joe-scotto/scottokeebs/Scotto63/README.md

# Scotto63 (SK25)

The Scotto63 is a 63-key 60% split-monoblock column-staggered ortholinear ergonomic wireless keyboard with a large 750mah battery.

You can read more about the components and how to build it [here](https://scottokeebs.com/blogs/keyboards/scotto63-handwired-keyboard).

Scotto63
