joe-scotto/scottokeebs/ScottoDeck/README.md

# ScottoDeck (SK24)

The ScottoDeck is an 8-key macropad with two EC11 encoders designed for live streaming.

You can read more about the components and how to build it [here](https://scottokeebs.com/blogs/macropads/scottodeck-handwired-macropad).

ScottoDeck
