joe-scotto/scottokeebs/ScottoNum/README.md

# ScottoNum (SK14)

The ScottoNum is a 17-key wireless macropad.

You can read more about the components and how to build it [here](https://scottokeebs.com/blogs/macropads/scottonum-handwired-macropad).

ScottoNum
