joe-scotto/scottokeebs/Extras/ScottoKicad/README.md

# ScottoKicad

A collection of footprints, symbols, and 3D models for building mechanical keyboards with Kicad.

```diff
- I used to recommend only using Kicad 8 but Kicad 10 is fine and fixed many issues that came up in 9.
- Please read all installation instructions carefully!
```
# Installation

1. Add a `SCOTTOKEEBS_KICAD` path to match where the `ScottoKicad` folder is located.
   Preferences -> Configure Paths
   Configure Paths

2. Add the symbol library.
   Preferences -> Manage Symbol Libraries
   Symbol Libraries

3. Add the footprint libraries.
   Preferences -> Manage Footprint Libraries
   Footprint Libraries      

4. Ensure hotkeys match tutorial.
   Settings
   Import hotkeys
   CleanShot 2025-06-30 at 11 00 42@2x
   
5. Match Scotto Configuration (Optional).
   Settings
   Reveal
   Preferences
   Theme

6. That's it, you should now have everything you need!

# Common grid sizes

-   18x17mm (Choc)
    -   1.00u - X: 18, Y:17
    -   0.50u - X: 9, Y: 8.5
    -   0.25u - X: 4.5, Y: 4.25
-   19.05x19.05 (MX/Alps)
    -   1.00u - X: 19.05, Y: 19.05
    -   0.50u - X: 9.525, Y: 9.525
    -   0.25u X: 4.7625, Y: 4.7625

# Common Shortcuts

-   **Add (A)** - Add a footprint or symbol.
-   **Set Origin Point (S)** - Set where everything else will move in relation to.
-   **Move with Reference (])** - Move a footprint with a reference point.
-   **Track Tool (X)** - Place traces
-   **Add Via (V)** - Place a via to run a trace between PCB layers.
-   **Flip (F)** - Switch footprint between back and front of the PCB.

# Resources

Please refer to each library in order to understand the license it uses, most are Creative Commons CC-BY-SA 4.0.

-   [Keyswitch Library](https://github.com/kiswitch/kiswitch/tree/main) - 3D models and footprints for switches, stabilizers, and sockets.
-   [Raspberry Pi Pico](https://github.com/ncarandini/KiCad-RP-Pico) - 3D model, footprint, and symbol.
-   [Arduino Pro Micro](https://github.com/g200kg/kicad-lib-arduino) - Footprint and symbol.
-   [Marbastlib](https://github.com/ebastler/marbastlib) - Symbols.
-   [Kleeb](https://github.com/crides/kleeb) - 3D models, symbols, and footprints.
-   [Keebio](https://github.com/keebio/Keebio-Parts.pretty) - 3D models, footprints, and symbols.
-   [Adafruit](https://github.com/adafruit/Adafruit_CAD_Parts/tree/main?tab=MIT-1-ov-file#readme) - 3D models

# Credits

Feel free to reach out to me on Discord if you want to help get a component into the library.

-   nice!nano - Base dimensions and placement by @Knotherface, can be found on GitHub as [Leopere](https://github.com/Leopere).
