joe-scotto/scottokeebs/ScottoRang/PCB/README.md

# ScottoRang (PCB Edition) (SK41)

The ScottoRang (PCB Edition) is a 34-key split monoblock ergonomic 16x16mm Choc spaced keyboard with a central 128x64 OLED display.

You can read more about the components and how to build it [here](https://scottokeebs.com/blogs/keyboards/scottorang-pcb-keyboard).

ScottoRang (PCB Editioin)

# Proudly Sponsored by [NextPCB](https://nextpcb.com)

Thanks to NextPCB for providing the PCBs for this project. Make sure to check them out for high quality PCB and PCBA services!
