joe-scotto/scottokeebs/ScottoT9/PCB/README.md

# ScottoT9 (SK39)

The ScottoT9 (PCB Edition) is a 14-key macropad based on the T9 keyboard layout with a 128x64 OLED display.

You can read more about the components and how to build it [here](https://scottokeebs.com/blogs/macropads/scottot9-pcb-macropad).

ScottoT9 (PCB Edition)

# Proudly Sponsored by [NextPCB](https://nextpcb.com)

Thanks to NextPCB for providing the PCBs for this project. Make sure to check them out for high quality PCB and PCBA services!
