joe-scotto/scottokeebs/Extras/ScottoShrink/README.md

# ScottoShrink

A tool for cutting perfect 8mm long pieces of heat shrink tubing.
