joe-scotto/scottokeebs/ScottoFrog/PCB/README.md

# ScottoFrog (SK37)

A 20-key single handed keyboard based on the [Frogpad](http://frogpad.com).

You can read more about the components and how to build it [here](https://scottokeebs.com/blogs/macropads/scottofrog-PCB-macropad).

ScottoFrog (PCB Edition

# Proudly Sponsored by [NextPCB](https://nextpcb.com)

Thanks to NextPCB for providing the PCBs for this project. Make sure to check them out for high quality PCB and PCBA services!
