joe-scotto/scottokeebs/ScottoT9/Handwired/README.md

# ScottoT9 (SK38)

The ScottoT9 is a 12-key macropad based on the T9 keyboard layout.

You can read more about the components and how to build it [here](https://scottokeebs.com/blogs/macropads/scottot9-handwired-macropad).

ScottoT9
