joe-scotto/scottokeebs/ScottoKatana/PCB/README.md

# ScottoKatana (PCB Edition) (SK35)

The ScottoKatana (PCB Edition) is a 35-key katana staggered keyboard with a 7u spacebar, 128x64 OLED, 6 RGB LEDs, and four 1.25u function keys.

You can read more about the components and how to build it [here](https://scottokeebs.com/blogs/keyboards/scottokatana-pcb-keyboard).

ScottoKatana (PCB Edition)

# Proudly Sponsored by [NextPCB](https://nextpcb.com)

Thanks to NextPCB for providing the PCBs for this project. Make sure to check them out for high quality PCB and PCBA services!
