joe-scotto/scottokeebs/Scotto69/PCB/README.md

# Scotto69 (PCB Edition) (SK30)

The Scotto69 (PCB Edition) is a standard 4x12 ortholinear keyboard with a numpad on the right and 5 macro keys on the left with an optional encoder.

You can read more about the components and how to build it [here](https://scottokeebs.com/blogs/keyboards/scotto69-pcb-keyboard).

Scotto69 (PCB Edition)
