joe-scotto/scottokeebs/ScottoSlant/PCB/README.md

# ScottoSlant (PCB Edition) (SK29)

The ScottoSlant is a 38-key 0.25u row-staggered keyboard with a split 2u spacebar.

You can read more about the components and how to build it [here](https://scottokeebs.com/blogs/keyboards/scottoslant-pcb-keyboard).

ScottoSlant (PCB Edition)
