joe-scotto/scottokeebs/Scotto34/PCB/README.md

# Scotto34 (PCB Edition) (SK19)

The Scotto34 (PCB Edition) is a low-profile 34-key split monoblock ortholinear keyboard that uses 18x17mm spaced Choc switches and an exposed controller in the middle.

You can read more about the components and how to build it [here](https://scottokeebs.com/blogs/keyboards/scotto34-pcb-keyboard).

Scotto34 (PCB Edition)
