joe-scotto/scottokeebs/ScottoWing/PCB/README.md

# ScottoWing (PCB Edition) (SK26)

The ScottoWing (PCB Edition) is a 3x5 (34-keys) or 3x6 (40-keys) split monoblock ergonomic column-staggered keyboard.

You can read more about the components and how to build it [here](https://scottokeebs.com/blogs/keyboards/scottowing-pcb-keyboard).

ScottoWing (PCB Edition)
