joe-scotto/scottokeebs/Extras/ScottoCoiler/README.md

# ScottoCoiler

Diode coiling jig for handwired builds. You will need [16g](https://amzn.to/3OyQrq8) wire in order to build it, along with some glue and [3x2mm round magnets](https://amzn.to/457QPnh). 

Alternatively, you can purchase a pre-built one [here](https://scottokeebs.com/products/diode-coiling-jig).

ScottoCoiler
