joe-scotto/scottokeebs/Extras/ScottoLube/README.md

# ScottoLube

ScottoLube

A lube station with space for 36 MX switches, just enough for most of my boards.
