joe-scotto/scottokeebs/ScottoAlp/KMK/README.md

# ScottoAlp

ScottoAlp

Please refer to the [ScottoAlp](https://github.com/joe-scotto/scottokeebs/tree/main/ScottoAlp) GitHub page for more information.

# Microcontroller Support

In `kb.py` file, replace `boardsource_blok` in the following line with a supported microcontroller listed in `kmk/quickpin/pro_micro`:

```python
from kmk.quickpin.pro_micro.boardsource_blok import pinout as pins
```
