joe-scotto/scottokeebs/Extras/ScottoCaps/Scooped/Readme.md

# ScottoCaps (Scooped)

Scooped Cherry MX and Choc keycaps designed for FDM 3D printing. The legend variant of these are specifically designed for a printer capable of dual extrusion, you cannot print the legends on a single extruder printer. I recommend putting the back of the keycap towards the build plate. By doing this, you'll hide any texture on the back of the cap where it won't be as visible.

-   **Legends:** Gotham Rounded (Bold)
-   **Legend Height:** ~6mm
-   **Legend Depth:** 1.6mm
-   **Blank Scoop:** 1.0mm
-   **Keycap Dimensions:** 18.3x18.3x7.4mm (17.5x16.5x4.8mm or 17.5x17.5x4.8mm) 
-   **Keycap Spacing:** 0.75mm (0.50mm Choc)
-   **Corner Fillet:** 1.25mm
-   **Top Fillet:** 0.625mm

ScottoCaps (Scooped) Bambu Studio

# Stems

The stems are designed based on a tolerance of ~0.15mm, your printer may or may not be capable of handling this. If your keycaps are too tight, you can use some hot water to make the plastic more pliable when installing them. If they are too loose, you can cut [Kapton tape](https://amzn.to/45GeFFr) and use it between the keycap and switch to improve the fit.

This same method will apply to the stabilizers and is more likely to be needed as they're not all made equal. I've found some stabilizers are a lot smaller than the Cherry MX stem specifications which in turn requires more than one piece of tape to get them properly attached.

**Don't force them onto your switches as if they're too tight, it will be very hard to get them off.**

Taped Stem
