joe-scotto/scottokeebs/ScottoWing/Handwired/QMK/readme.md

# ScottoWing

ScottoWing

A low-profile 34/40-key split monoblock ergonomic column-staggered ortholinear keyboard that uses 18x17mm spaced Choc switches.

*   Keyboard Maintainer: [Joe Scotto](https://github.com/joe-scotto)
*   Hardware Supported: RP2040 ero
*   Hardware Availability: [ScottoKeebs](https://scottokeebs.com), [Amazon](https://amazon.com), [AliExpress](https://aliexpress.com)

# Compiling

Make example for this keyboard (after setting up your build environment):

    make scottokeebs/handwired/scottowing:default

Flashing example for this keyboard:

    make scottokeebs/handwired/scottowing:default:flash

See the [build environment setup](https://docs.qmk.fm/#/getting_started_build_tools) and the [make instructions](https://docs.qmk.fm/#/getting_started_make_guide) for more information. Brand new to QMK? Start with our [Complete Newbs Guide](https://docs.qmk.fm/#/newbs).

# Bootloader

Enter the bootloader in 3 ways:

*   **Bootmagic reset**: Hold down the key at (0,1) in the matrix (usually the top left key or Escape) and plug in the keyboard
*   **Physical reset button**: Briefly press the button on the back of the PCB - some may have pads you must short instead
*   **Keycode in layout**: Press the key mapped to `QK_BOOT` if it is available
