joe-scotto/scottokeebs/Extras/ScottoCaps/Glass/README.md

# ScottoCaps (Glass)

Low-profile flat keycaps designed for MSLA 3D printing compatible with MX and Choc switches. Designed to print flat on the build plate and tolerances may require modification depending on your printer.

**These must be printed in a bio-compatible 3D printing resin such as [Siraya Tech Blu](https://amzn.to/3seh5Nt)**

ScottoCaps on Scotto34 (PCB Edition)
