joe-scotto/scottokeebs/ScottoErgo/README.md

# ScottoErgo (SK16)

The ScottoErgo a 36-key column staggered ortholinear ergonomic keyboard with an exposed controller, aviator connector for USB, 10° of tilt, and 20° of angle.

You can read more about the components and how to build it [here](https://scottokeebs.com/blogs/keyboards/scottoergo-handwired-keyboard).

ScottoErgo
