joe-scotto/scottokeebs/ScottoGame/README.md

# ScottoGame (SK6)

The ScottoGame is a 42-key ortholinear keyboard with a dedicated action button, split spacebar, 5 function keys, and a 0.96" 128x64 OLED display.

You can read more about the components and how to build it [here](https://scottokeebs.com/blogs/keyboards/scottogame-handwired-keyboard).

ScottoGame
