joe-scotto/scottokeebs/ScottoSplit/README.md

# ScottoSplit (SK12)

The ScottoSplit is a 36-key split column-staggered ortholinear keyboard that uses a single MCU and VGA cable to connect the halves.

You can read more about the components and how to build it [here](https://scottokeebs.com/blogs/keyboards/scottosplit-handwired-keyboard).

ScottoSplit
