joe-scotto/scottokeebs/Scotto34/Handwired/README.md

# Scotto34 (SK13)

The Scotto34 is a low-profile 34-key split monoblock ortholinear keyboard that uses 18x17mm spaced Choc switches and an exposed controller in the middle.

You can read more about the components and how to build it [here](https://scottokeebs.com/blogs/keyboards/Scotto34-handwired-keyboard).

Scotto34
