joe-scotto/scottokeebs/Extras/ScottoCaps/Scooped/MX/Legends/Shift (1.50u).3mf

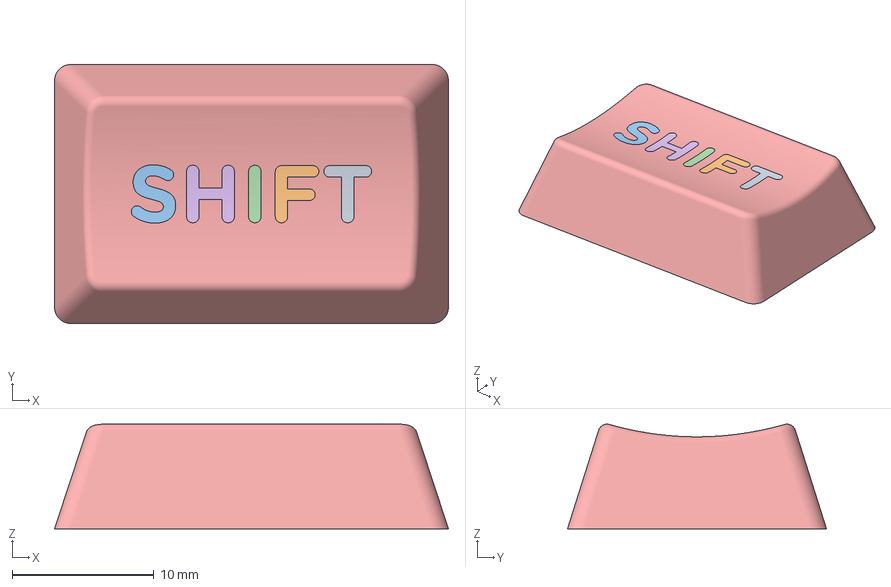
[picture p19: CAD file, 2024-05-18]
Extras/ScottoCaps/Scooped/MX/Legends/Shift (1.50u).3mf
27.8 x 18.3 x 7.39 mm
T
F
S
I
Keycap
H
