joe-scotto/scottokeebs/Extras/ScottoCaps/Scooped/MX/Raw/Concave Cutter.step

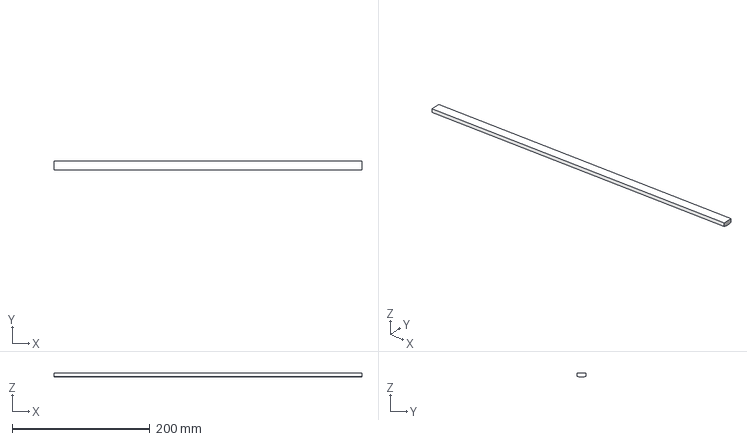
[picture p20: CAD file, 2026-04-09]
Extras/ScottoCaps/Scooped/MX/Raw/Concave Cutter.step
446.9 x 13.3 x 6.00 mm
