joe-scotto/scottokeebs/Extras/ScottoCaps/Scooped/MX/ScottoCaps (Scooped - MX) - Raw.step

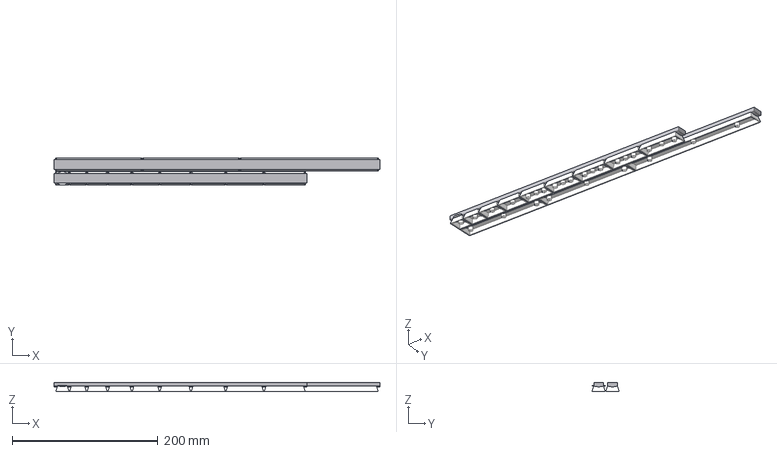
[picture p21: CAD file, 2023-12-27]
Extras/ScottoCaps/Scooped/MX/ScottoCaps (Scooped - MX) - Raw.step
446.9 x 37.5 x 12.5 mm
