joe-scotto/scottokeebs/Extras/ScottoCaps/ScottoCaps - 2.50u.step

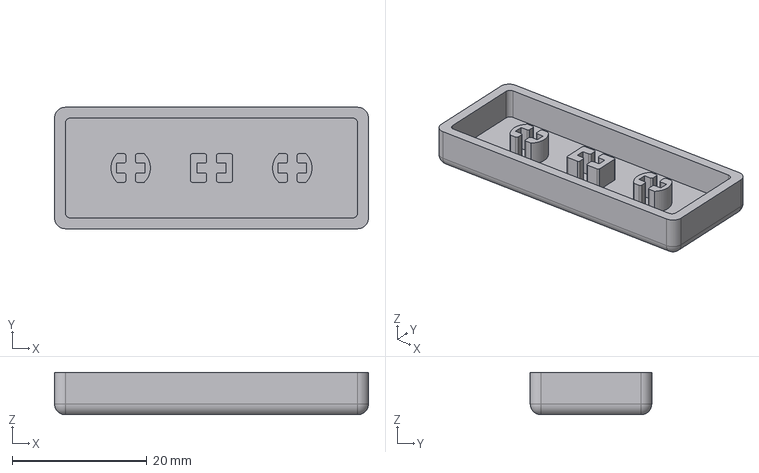
[picture p22: CAD file, 2023-07-28]
Extras/ScottoCaps/ScottoCaps - 2.50u.step
46.6 x 18.0 x 6.30 mm
