joe-scotto/scottokeebs/Extras/ScottoCaps/Sculpted/Blanks/R2 - 7.00u.step

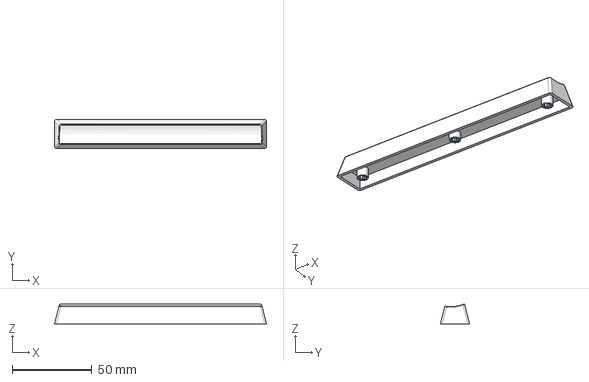
[picture p23: CAD file, 2025-02-17]
Extras/ScottoCaps/Sculpted/Blanks/R2 - 7.00u.step
132.6 x 18.3 x 12.4 mm
