joe-scotto/scottokeebs/Extras/ScottoCaps/Standard/ScottoCaps (Standard) - 10.00u.step

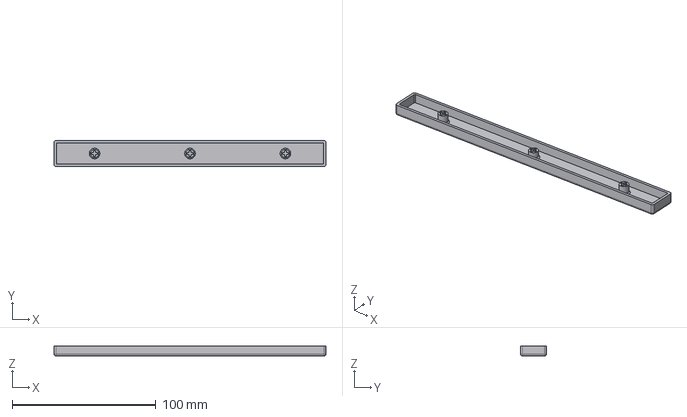
[picture p24: CAD file, 2023-10-19]
Extras/ScottoCaps/Standard/ScottoCaps (Standard) - 10.00u.step
189.5 x 18.0 x 6.90 mm
