joe-scotto/scottokeebs/Extras/ScottoCoiler/ScottoCoiler - Top.step

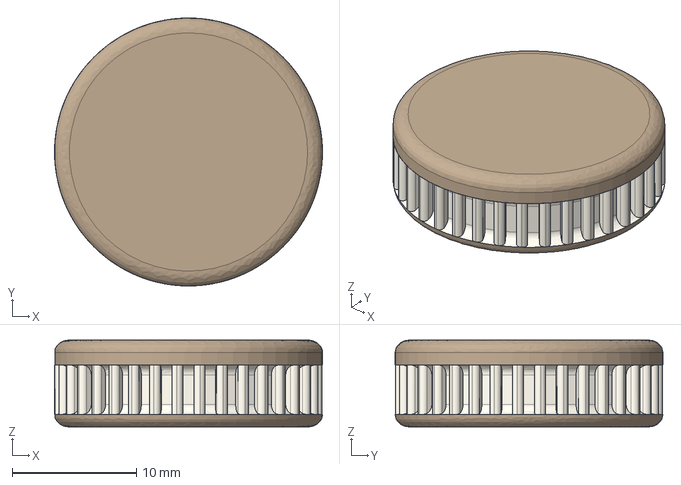
[picture p25: CAD file, 2024-01-28]
Extras/ScottoCoiler/ScottoCoiler - Top.step
21.6 x 21.6 x 7.00 mm
