joe-scotto/scottokeebs/Extras/ScottoCyberdeck/Case/ScottoCyberdeck.step

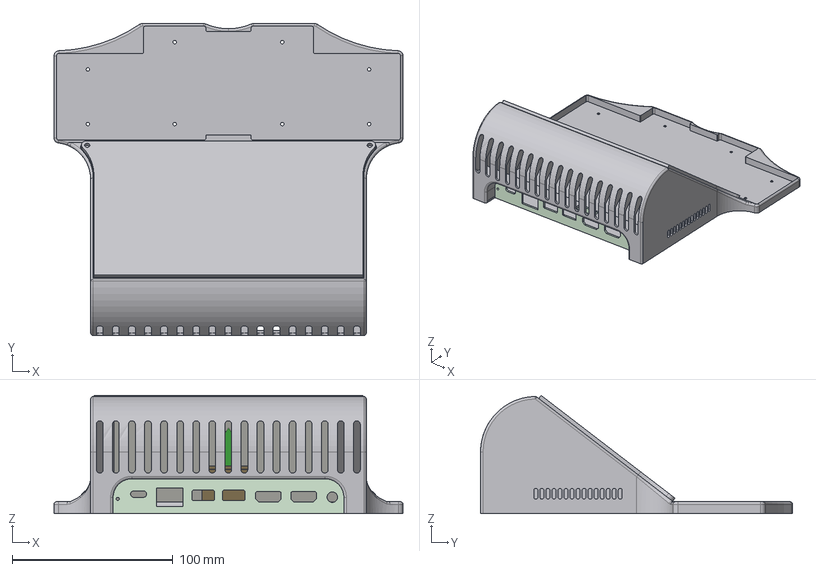
[picture p26: CAD file, 2024-12-17]
Extras/ScottoCyberdeck/Case/ScottoCyberdeck.step
217.2 x 194.2 x 73.5 mm
