joe-scotto/scottokeebs/Extras/ScottoHousing/ScottoHousing - Housing (USB-C).step

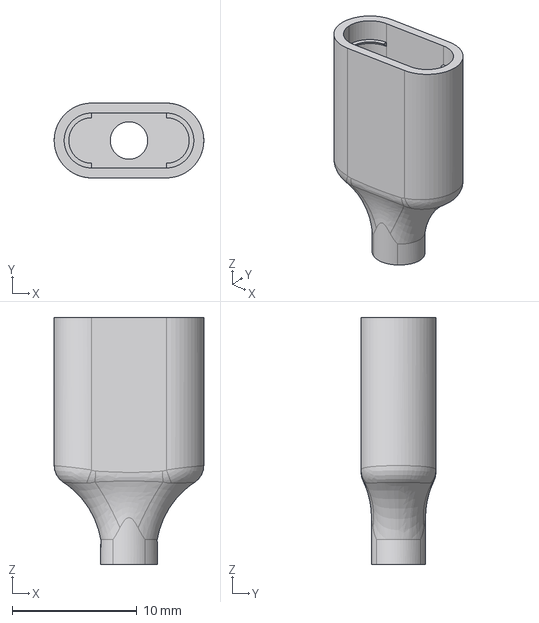
[picture p27: CAD file, 2025-08-10]
Extras/ScottoHousing/ScottoHousing - Housing (USB-C).step
12.0 x 6.00 x 19.8 mm
