joe-scotto/scottokeebs/Extras/ScottoLube/ScottoLube.step

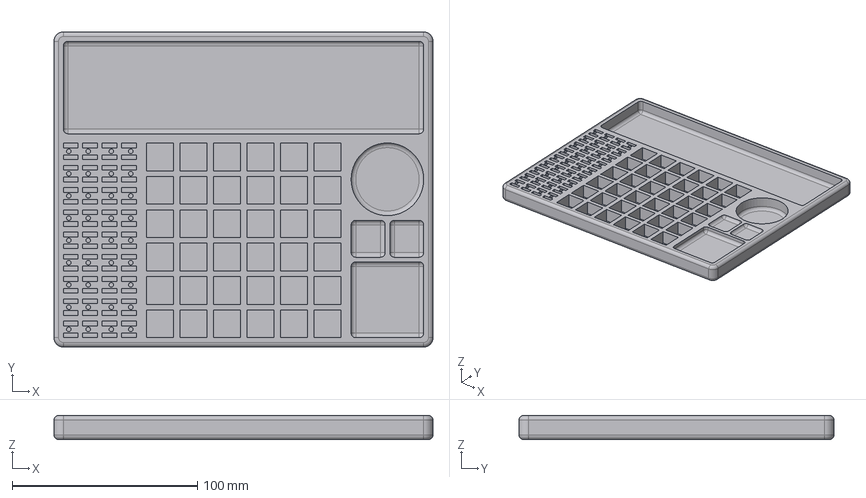
[picture p28: CAD file, 2024-01-22]
Extras/ScottoLube/ScottoLube.step
204.8 x 170.3 x 13.0 mm
