joe-scotto/scottokeebs/Extras/ScottoOpener/ScottoOpener - Cherry (Flat).step

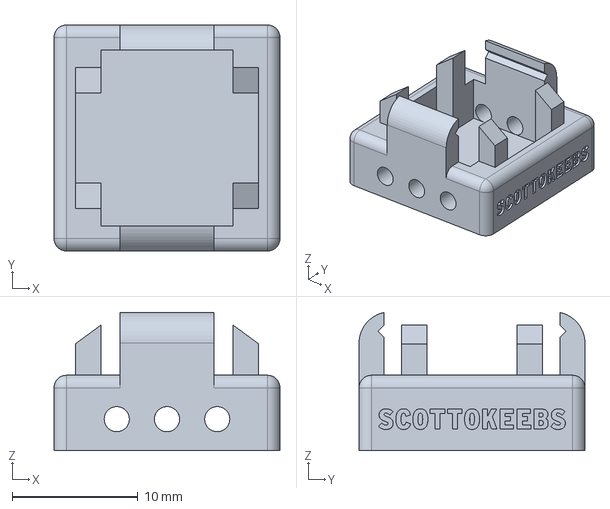
[picture p29: CAD file, 2023-08-27]
Extras/ScottoOpener/ScottoOpener - Cherry (Flat).step
18.0 x 18.0 x 11.0 mm
