joe-scotto/scottokeebs/Extras/ScottoShrink/ScottoShrink - Lid.step

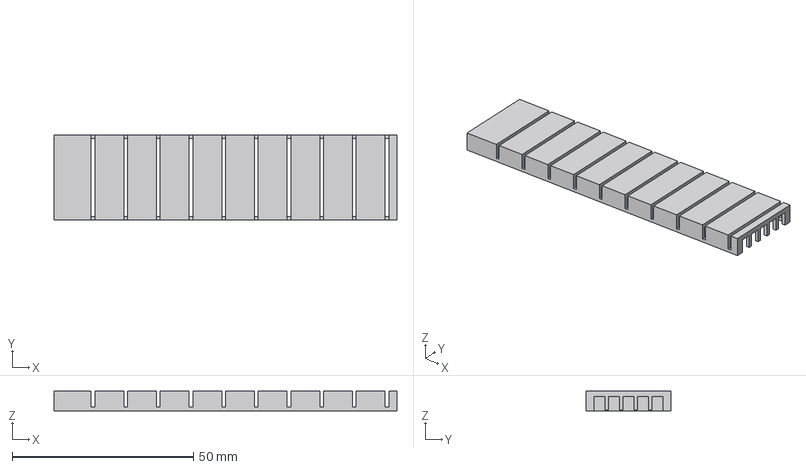
[picture p30: CAD file, 2025-12-25]
Extras/ScottoShrink/ScottoShrink - Lid.step
94.5 x 23.5 x 5.40 mm
