joe-scotto/scottokeebs/Scotto108/Case/Scotto108 - Case (Bottom).step

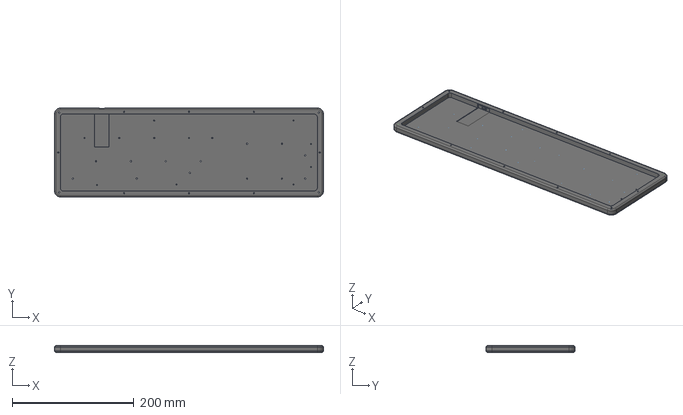
[picture p31: CAD file, 2026-04-20]
Scotto108/Case/Scotto108 - Case (Bottom).step
441.1 x 145.8 x 11.0 mm
