joe-scotto/scottokeebs/Scotto16/Case/Scotto16 - Plate.step

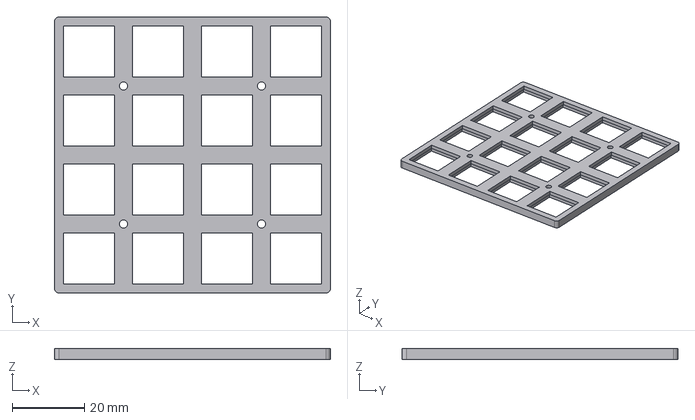
[picture p32: CAD file, 2025-05-08]
Scotto16/Case/Scotto16 - Plate.step
76.2 x 76.2 x 3.00 mm
