joe-scotto/scottokeebs/Scotto2/Case/Scotto2 - Plate.step

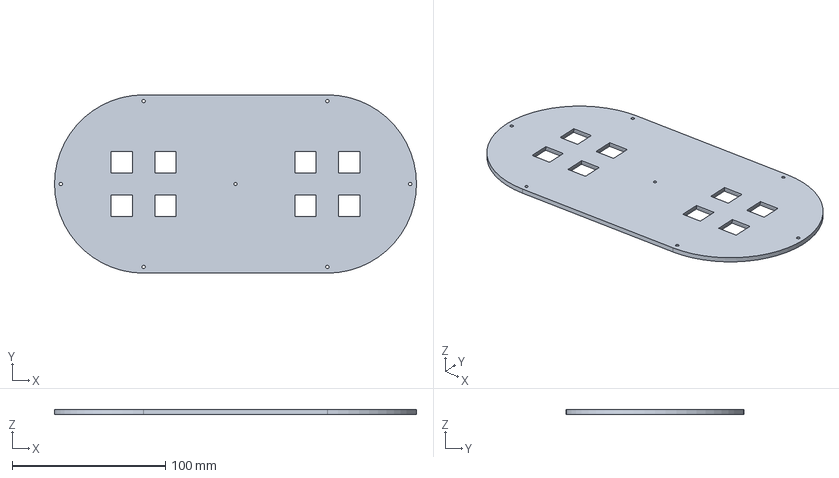
[picture p33: CAD file, 2026-05-15]
Scotto2/Case/Scotto2 - Plate.step
236.5 x 116.5 x 3.00 mm
