joe-scotto/scottokeebs/Scotto20/Case/Scotto20 - Case.step

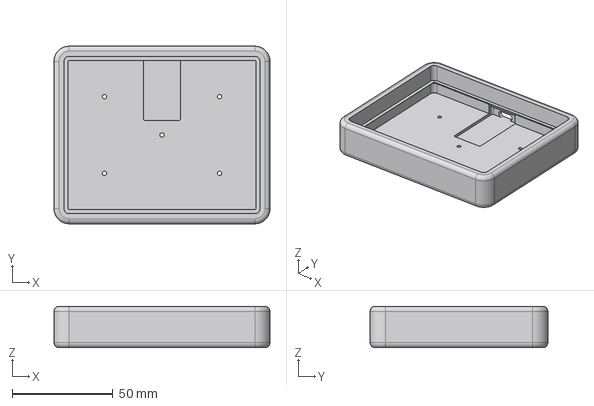
[picture p34: CAD file, 2025-07-22]
Scotto20/Case/Scotto20 - Case.step
107.2 x 88.2 x 20.6 mm
