joe-scotto/scottokeebs/Scotto26/Case/Scotto26 - Spacebar.step

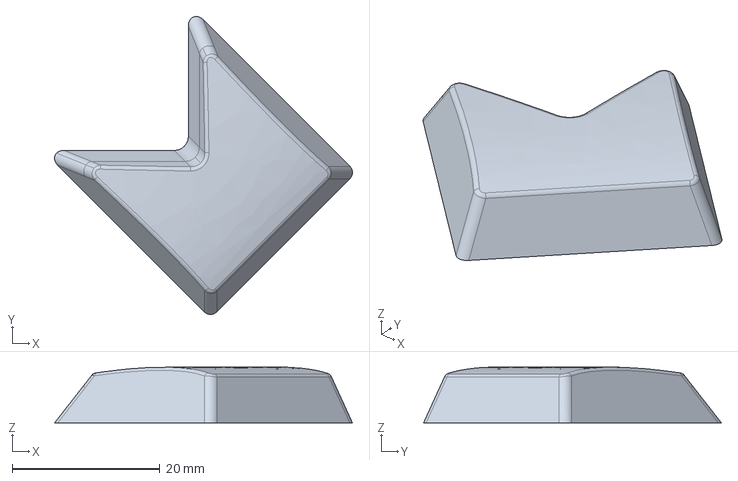
[picture p35: CAD file, 2026-09-21]
Scotto26/Case/Scotto26 - Spacebar.step
40.3 x 40.3 x 7.55 mm
