joe-scotto/scottokeebs/Scotto34/Handwired/Case/Scotto34 - Bottom (V2).step

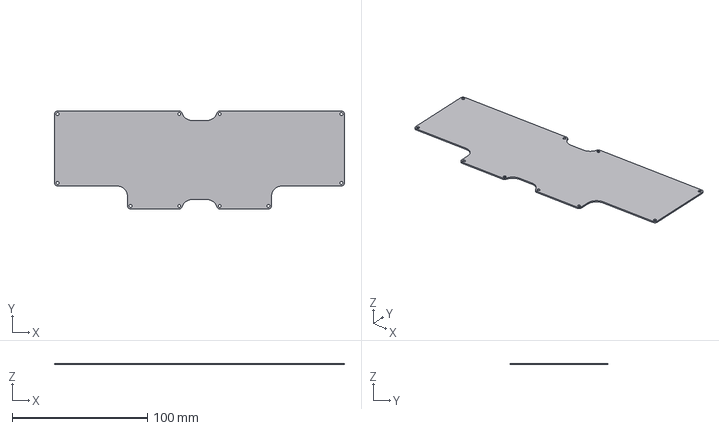
[picture p36: CAD file, 2025-06-09]
Scotto34/Handwired/Case/Scotto34 - Bottom (V2).step
214.5 x 72.5 x 1.00 mm
