joe-scotto/scottokeebs/Scotto34/PCB/Case/Choc V2 - Keycaps.3mf

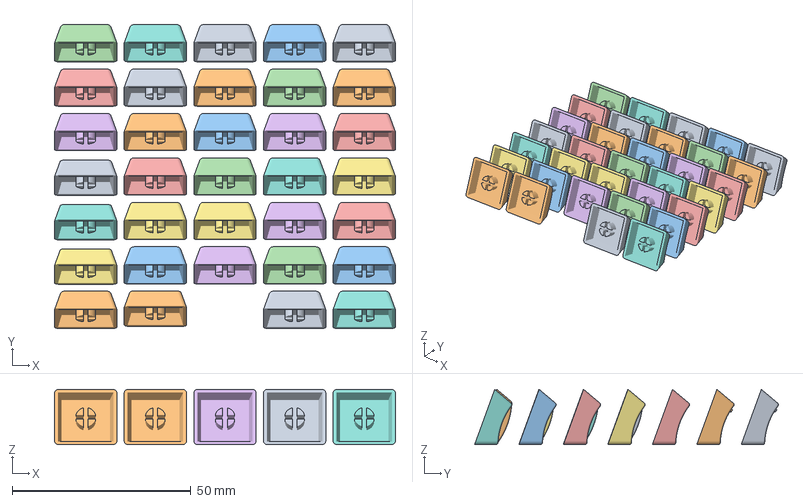
[picture p37: CAD file, 2026-10-05]
Scotto34/PCB/Case/Choc V2 - Keycaps.3mf
95.5 x 85.1 x 15.5 mm
Choc V2 - 1.00u (Homing).stl x 2
Choc V2 - 1.00u (Concave).stl x 28
Choc V2 - 1.00u (Convex).stl x 4
