joe-scotto/scottokeebs/Scotto34/PCB/Case/Keycaps/Choc V2 - 1.00u (Homing).step

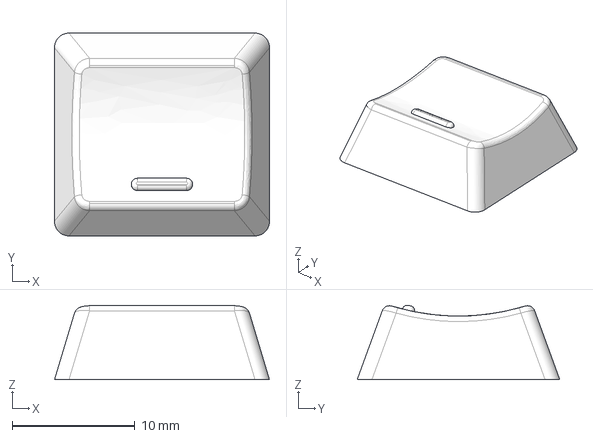
[picture p38: CAD file, 2026-10-05]
Scotto34/PCB/Case/Keycaps/Choc V2 - 1.00u (Homing).step
17.5 x 16.5 x 6.06 mm
