joe-scotto/scottokeebs/Scotto36/Case/Scotto36 - Plate.step

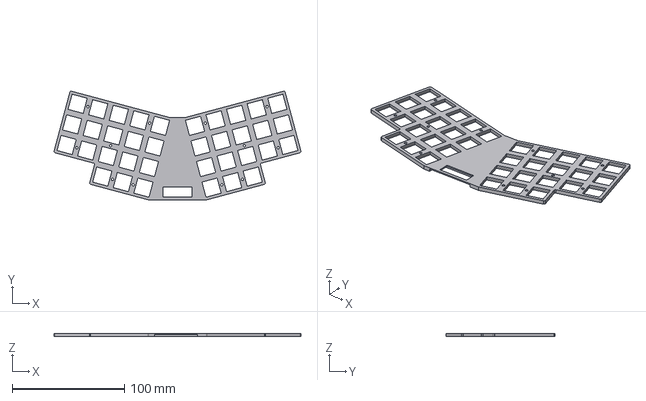
[picture p39: CAD file, 2023-06-10]
Scotto36/Case/Scotto36 - Plate.step
220.3 x 96.9 x 3.00 mm
