joe-scotto/scottokeebs/Scotto37/Case/Scotto37 - Bottom (2mm Gasket - ScottoKeebs).step

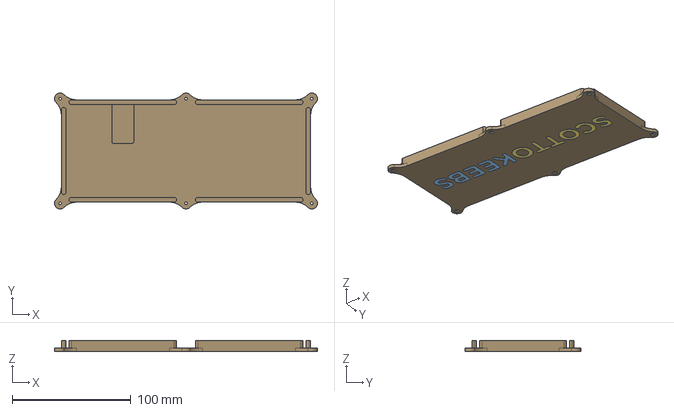
[picture p40: CAD file, 2024-06-03]
Scotto37/Case/Scotto37 - Bottom (2mm Gasket - ScottoKeebs).step
221.5 x 97.7 x 9.20 mm
Scotto (Yellow)
Keebs (Blue)
