joe-scotto/scottokeebs/Scotto40/Case/Scotto40 - Case (RP2040).step

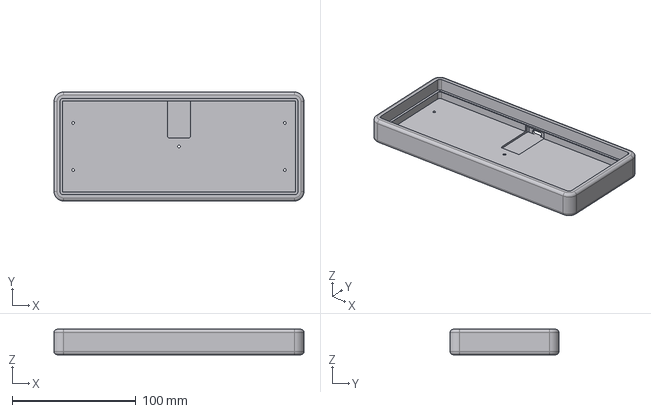
[picture p41: CAD file, 2025-12-25]
Scotto40/Case/Scotto40 - Case (RP2040).step
201.8 x 87.8 x 20.6 mm
