joe-scotto/scottokeebs/Scotto44/Case/Scotto44 - Case (3x6).step

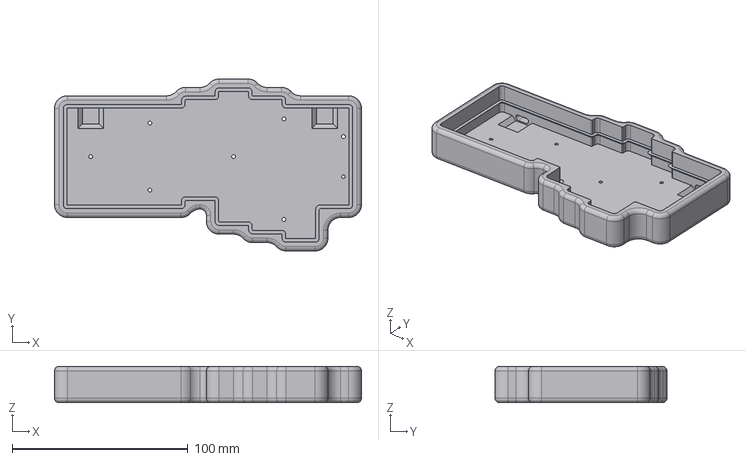
[picture p42: CAD file, 2024-12-22]
Scotto44/Case/Scotto44 - Case (3x6).step
174.5 x 97.7 x 20.6 mm
