joe-scotto/scottokeebs/Scotto48/PCB/Case/Scotto48 - Keycaps (Blanks).3mf

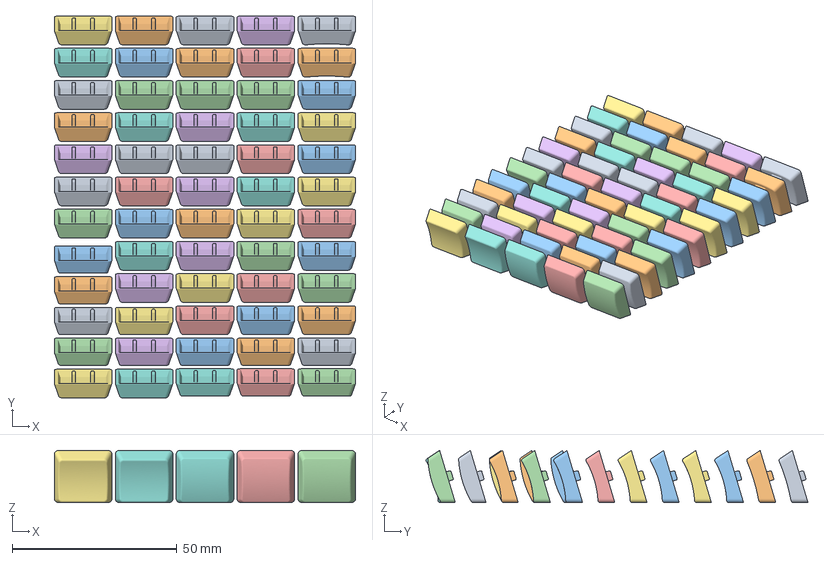
[picture p43: CAD file, 2026-06-23]
Scotto48/PCB/Case/Scotto48 - Keycaps (Blanks).3mf
91.5 x 116.0 x 15.8 mm
1.00u (18x17 - Homing - Domed).step x 2
1.00u (18x17 - Concave).step x 46
1.00u (18x17 - Convex).step x 12
