joe-scotto/scottokeebs/Scotto55/Case/Scotto55 - Plate.step

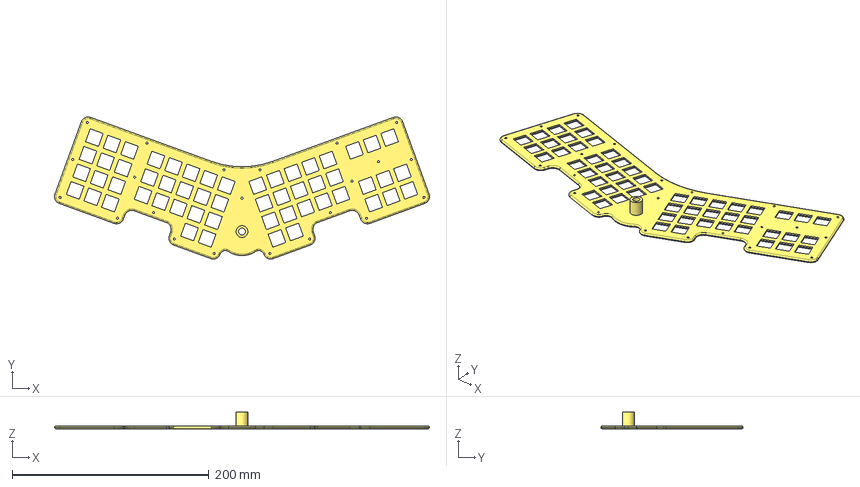
[picture p44: CAD file, 2026-03-06]
Scotto55/Case/Scotto55 - Plate.step
381.6 x 144.6 x 17.0 mm
