joe-scotto/scottokeebs/Scotto61/Case/Scotto61 - Case (Bottom).step

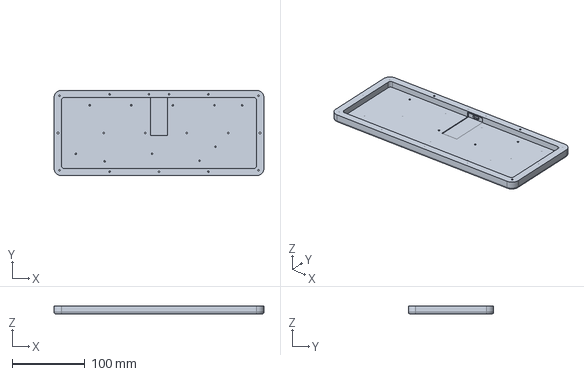
[picture p45: CAD file, 2023-12-15]
Scotto61/Case/Scotto61 - Case (Bottom).step
288.7 x 117.2 x 11.0 mm
