joe-scotto/scottokeebs/Scotto63/Case/Scotto63 - Cover (Text).step

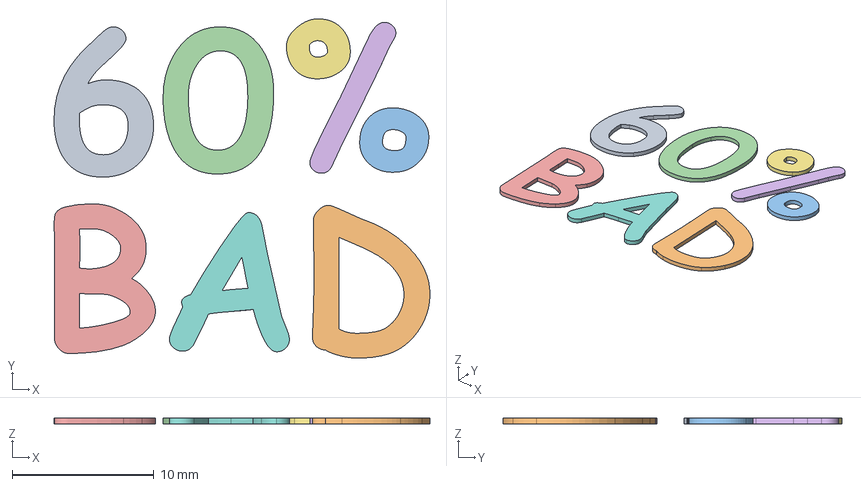
[picture p46: CAD file, 2024-02-19]
Scotto63/Case/Scotto63 - Cover (Text).step
26.5 x 24.0 x 0.4 mm
