joe-scotto/scottokeebs/Scotto69/PCB/Case/Scotto69 (PCB Edition) - Case (Bottom).step

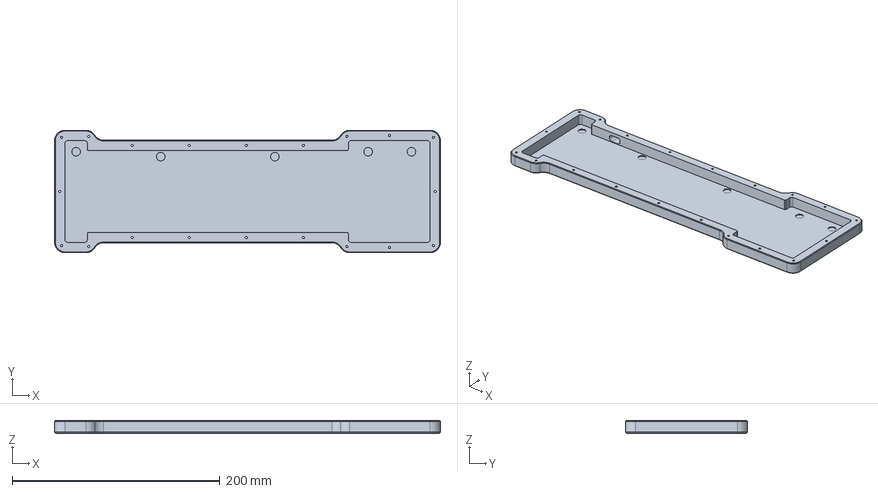
[picture p47: CAD file, 2025-03-08]
Scotto69/PCB/Case/Scotto69 (PCB Edition) - Case (Bottom).step
371.4 x 117.8 x 12.4 mm
