joe-scotto/scottokeebs/Scotto9/Case/Scotto9 - Plate.step

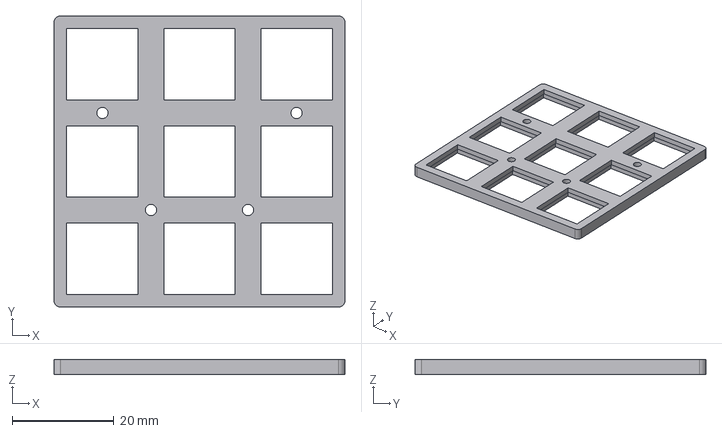
[picture p48: CAD file, 2026-04-25]
Scotto9/Case/Scotto9 - Plate.step
57.1 x 57.1 x 3.00 mm
