joe-scotto/scottokeebs/ScottoAlp/Case/ScottoAlp - Case (4x12_7).step

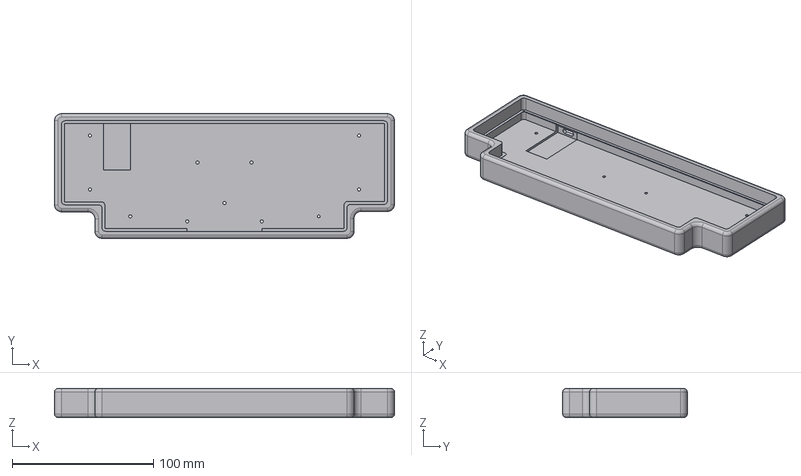
[picture p49: CAD file, 2024-01-08]
ScottoAlp/Case/ScottoAlp - Case (4x12_7).step
240.6 x 88.2 x 20.6 mm
