joe-scotto/scottokeebs/ScottoBigum/Case/ScottoBigum - Keycaps.step

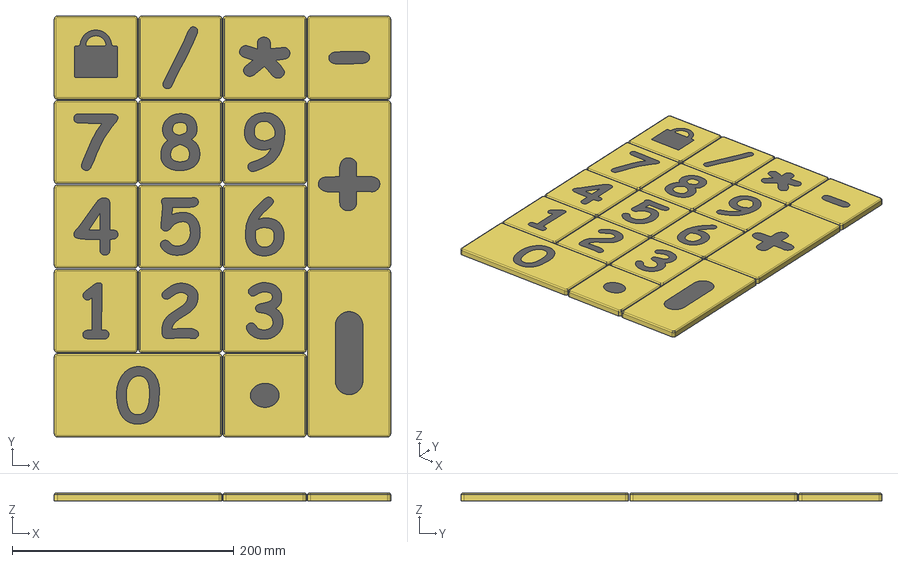
[picture p50: CAD file, 2026-07-09]
ScottoBigum/Case/ScottoBigum - Keycaps.step
303.8 x 380.0 x 7.10 mm
Lock
Period
Enter
Plus
Minus
Asterisk
Slash
