joe-scotto/scottokeebs/ScottoChoczard/Case/ScottoChoczard - Design.step

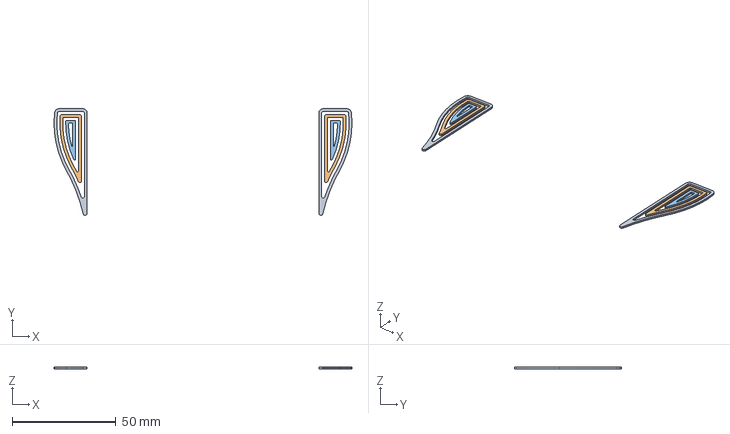
[picture p51: CAD file, 2024-10-28]
ScottoChoczard/Case/ScottoChoczard - Design.step
143.9 x 51.5 x 0.8 mm
Left
Right
