joe-scotto/scottokeebs/ScottoCirque/Case/ScottoCirque - Top.step

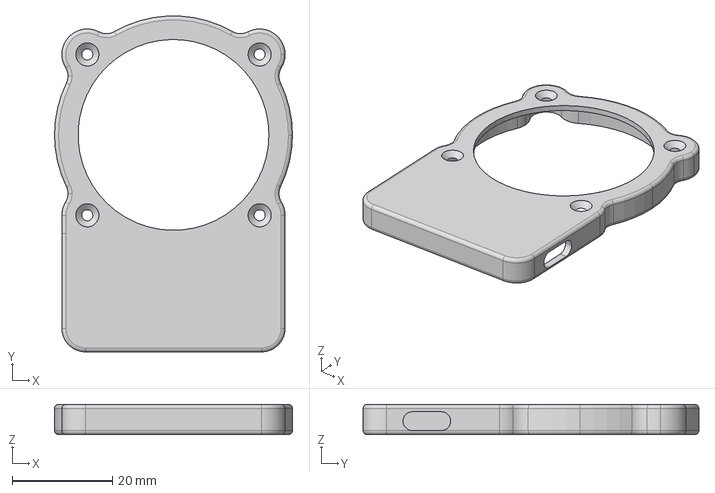
[picture p52: CAD file, 2026-08-07]
ScottoCirque/Case/ScottoCirque - Top.step
47.4 x 66.9 x 6.00 mm
