joe-scotto/scottokeebs/ScottoCMD/Case/ScottoCMD - Plate.step

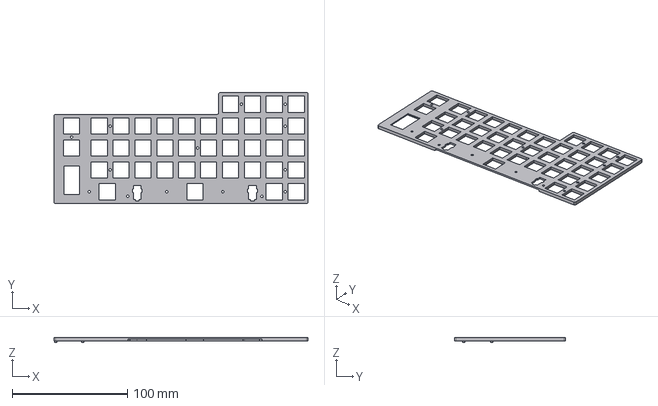
[picture p53: CAD file, 2023-06-13]
ScottoCMD/Case/ScottoCMD - Plate.step
220.5 x 96.5 x 4.50 mm
