joe-scotto/scottokeebs/ScottoErgo/Case/ScottoErgo - Case.step

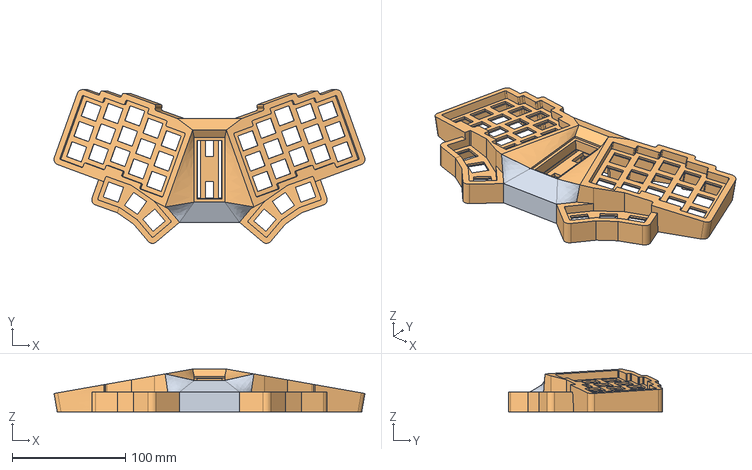
[picture p54: CAD file, 2024-11-01]
ScottoErgo/Case/ScottoErgo - Case.step
274.4 x 135.7 x 37.9 mm
