joe-scotto/scottokeebs/ScottoFly/Case/ScottoFly - Plate.step

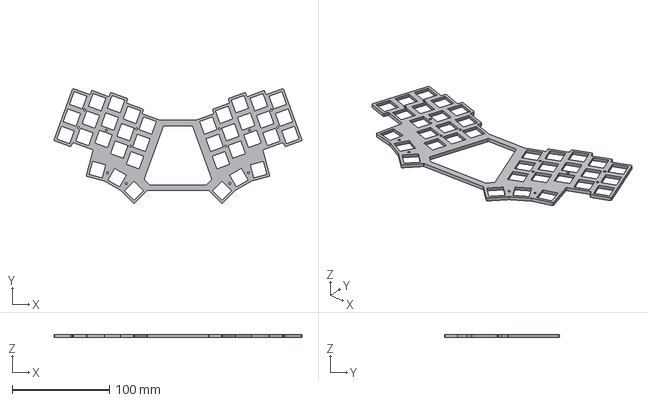
[picture p55: CAD file, 2023-06-14]
ScottoFly/Case/ScottoFly - Plate.step
255.6 x 118.2 x 3.00 mm
