joe-scotto/scottokeebs/ScottoFrog/Case/ScottoFrog - Case.step

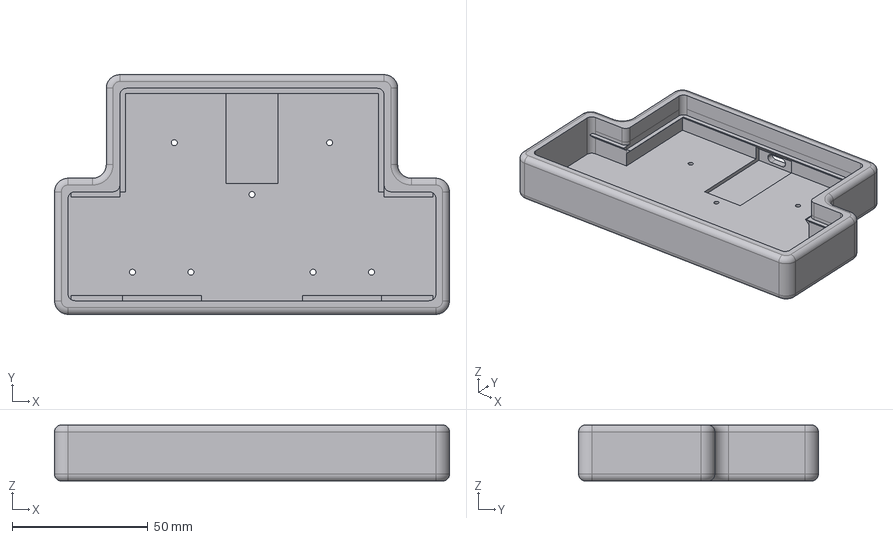
[picture p56: CAD file, 2023-06-13]
ScottoFrog/Case/ScottoFrog - Case.step
145.3 x 88.2 x 20.6 mm
