joe-scotto/scottokeebs/ScottoFrog/Handwired/Case/ScottoFrog - Plate (RP2040 Pro Micro) - CNC.step

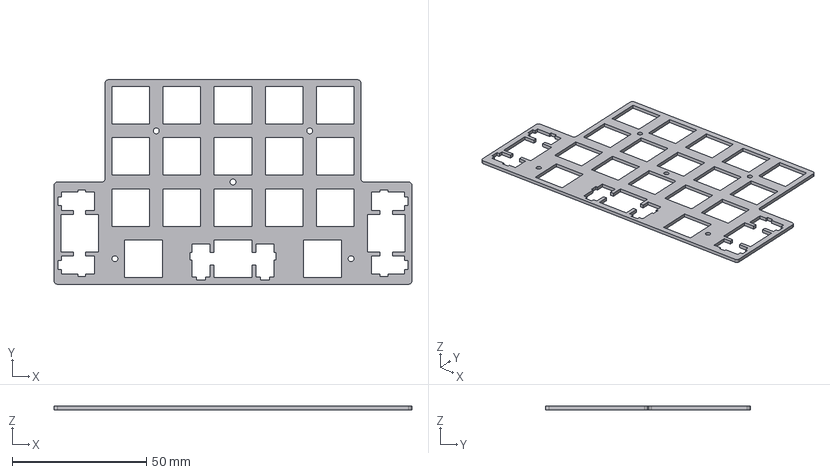
[picture p57: CAD file, 2025-04-22]
ScottoFrog/Handwired/Case/ScottoFrog - Plate (RP2040 Pro Micro) - CNC.step
133.3 x 76.2 x 1.40 mm
