joe-scotto/scottokeebs/ScottoGame/Case/ScottoGame - Case.step

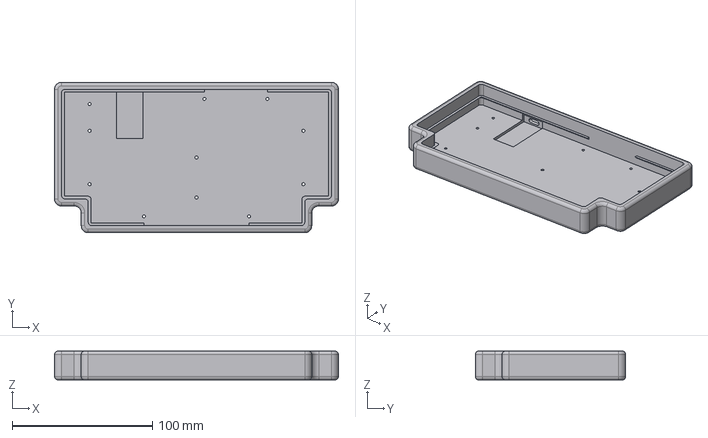
[picture p58: CAD file, 2023-06-12]
ScottoGame/Case/ScottoGame - Case.step
202.5 x 107.3 x 20.6 mm
