joe-scotto/scottokeebs/ScottoInvader/Case/ScottoInvader - Plate.step

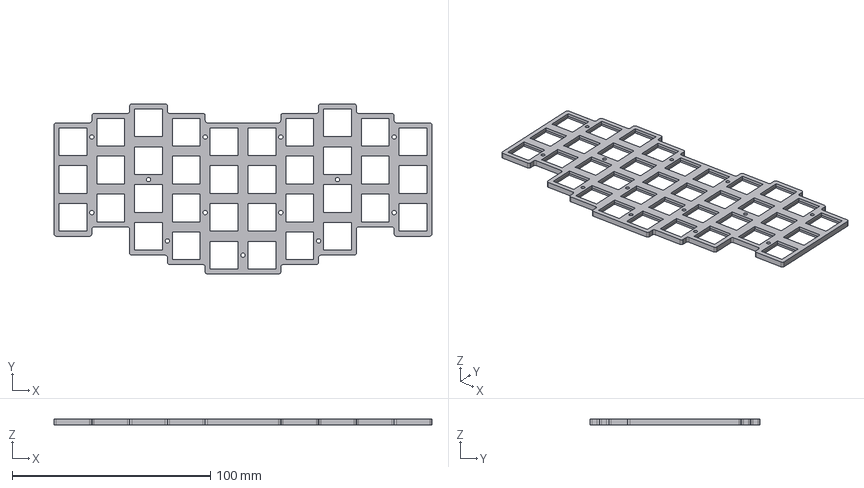
[picture p59: CAD file, 2023-06-10]
ScottoInvader/Case/ScottoInvader - Plate.step
190.5 x 85.8 x 3.00 mm
