joe-scotto/scottokeebs/ScottoKatana/Case/ScottoKatana - Gasket Plate.step

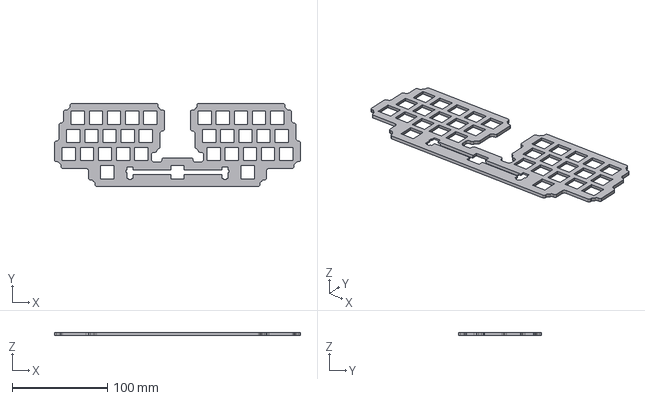
[picture p60: CAD file, 2024-01-02]
ScottoKatana/Case/ScottoKatana - Gasket Plate.step
258.6 x 87.2 x 3.00 mm
