joe-scotto/scottokeebs/ScottoKatana/PCB/Case/ScottoKatana (PCB Edition) - PCB Cover.step

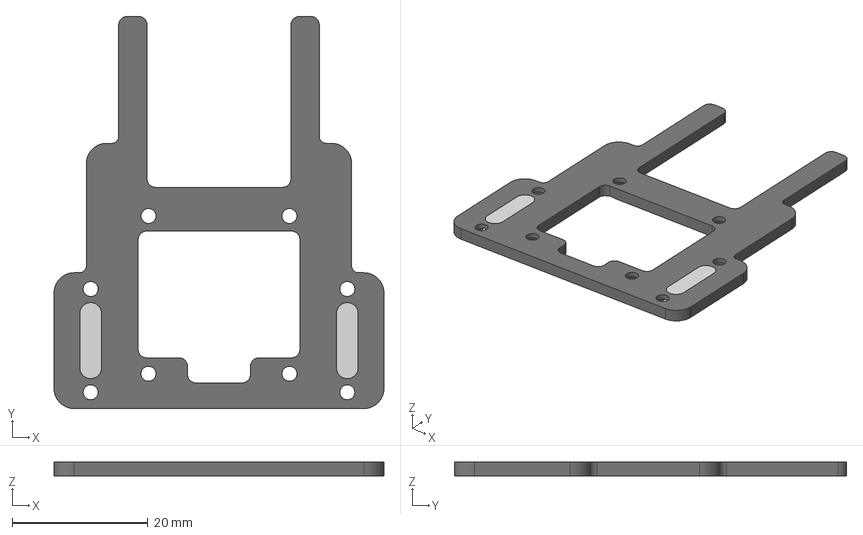
[picture p61: CAD file, 2025-08-03]
ScottoKatana/PCB/Case/ScottoKatana (PCB Edition) - PCB Cover.step
48.6 x 57.7 x 2.00 mm
