joe-scotto/scottokeebs/ScottoLong/Handwired/Case/ScottoLong_Plate (7u Spacebar).step

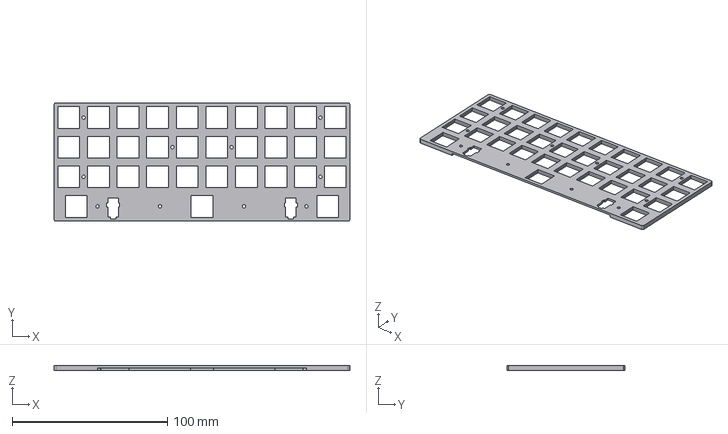
[picture p62: CAD file, 2024-05-23]
ScottoLong/Handwired/Case/ScottoLong_Plate (7u Spacebar).step
190.5 x 76.2 x 3.00 mm
