joe-scotto/scottokeebs/ScottoLong/PCB/Case/ScottoLong (PCB Edition) - Plate.step

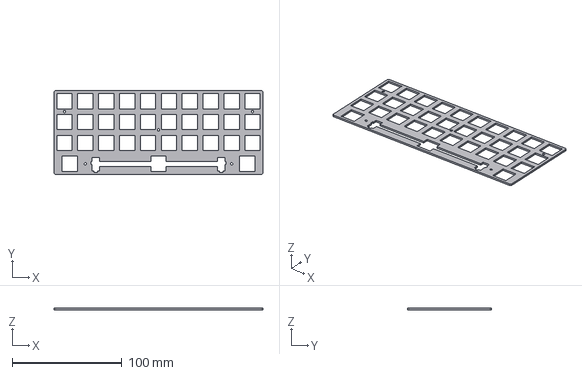
[picture p63: CAD file, 2024-07-18]
ScottoLong/PCB/Case/ScottoLong (PCB Edition) - Plate.step
190.5 x 76.2 x 1.50 mm
