joe-scotto/scottokeebs/ScottoMacrodeck/Case/ScottoMacrodeck - Bottom.step

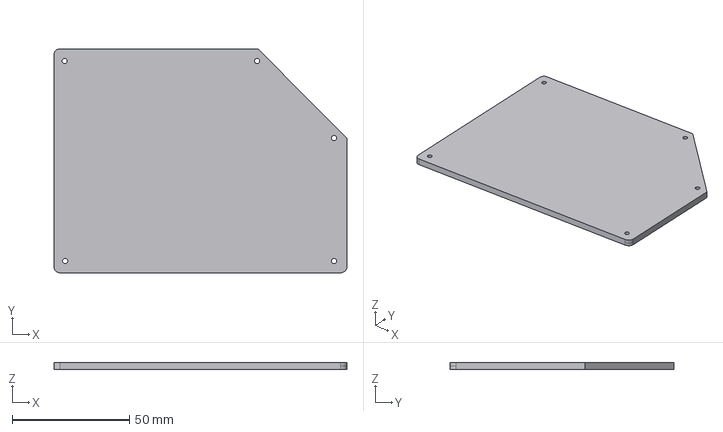
[picture p64: CAD file, 2023-06-10]
ScottoMacrodeck/Case/ScottoMacrodeck - Bottom.step
124.7 x 95.2 x 3.00 mm
