joe-scotto/scottokeebs/ScottoMouse/Case/ScottoMouse - Plate.step

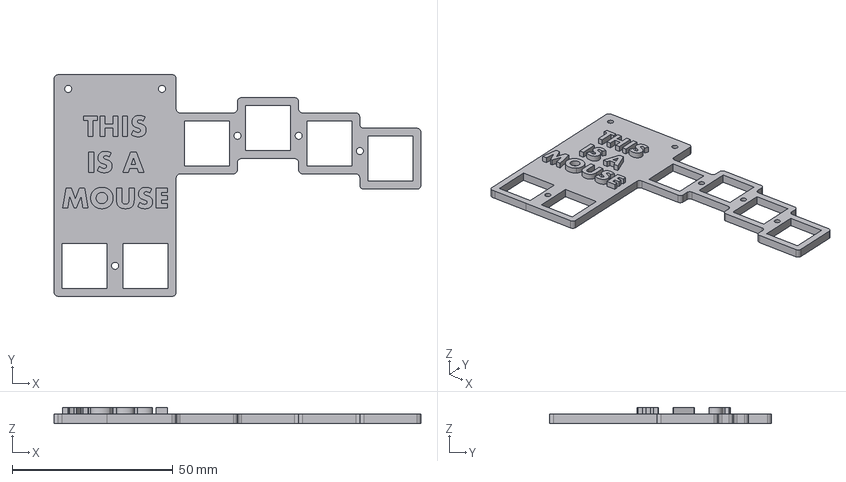
[picture p65: CAD file, 2023-06-10]
ScottoMouse/Case/ScottoMouse - Plate.step
114.2 x 69.0 x 5.00 mm
