joe-scotto/scottokeebs/ScottoNum/Case/ScottoNum - Bottom.step

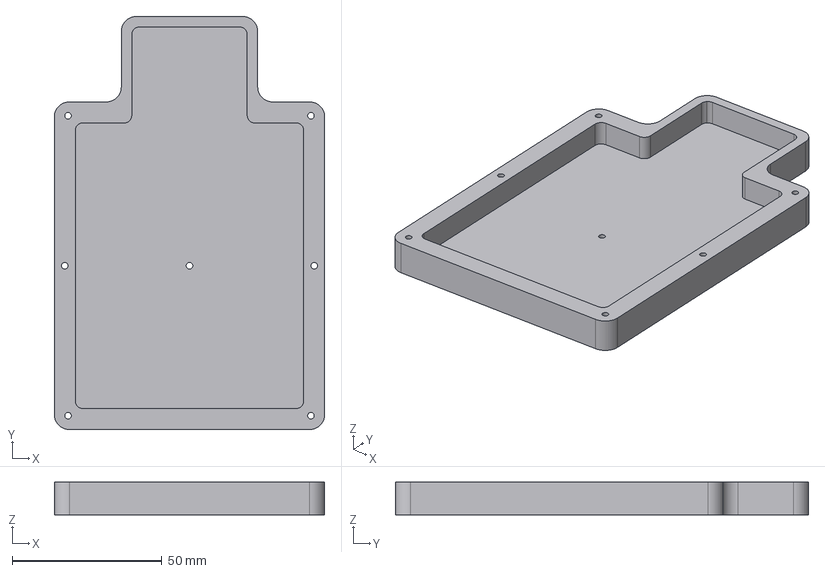
[picture p66: CAD file, 2023-06-11]
ScottoNum/Case/ScottoNum - Bottom.step
90.2 x 137.7 x 11.0 mm
