joe-scotto/scottokeebs/ScottoPad/Case/ScottoPad - Case.step

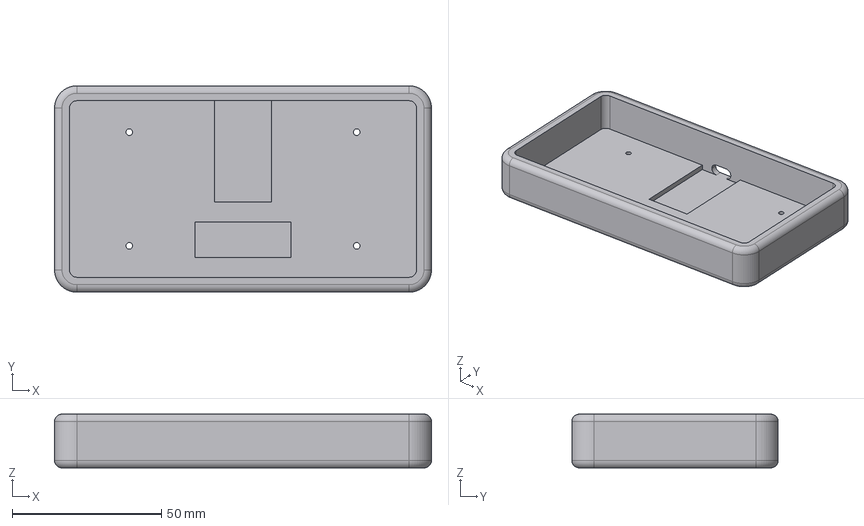
[picture p67: CAD file, 2025-04-05]
ScottoPad/Case/ScottoPad - Case.step
126.3 x 69.2 x 18.0 mm
