joe-scotto/scottokeebs/ScottoRang/Handwired/Case/ScottoRang - Case.step

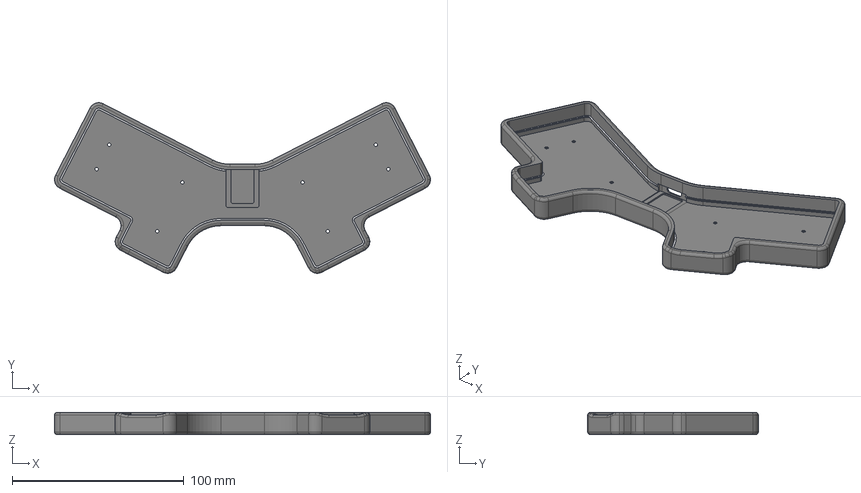
[picture p68: CAD file, 2026-01-11]
ScottoRang/Handwired/Case/ScottoRang - Case.step
219.2 x 99.5 x 13.0 mm
