joe-scotto/scottokeebs/ScottoRang/PCB/Case/ScottoRang (PCB Edition) - Case.step

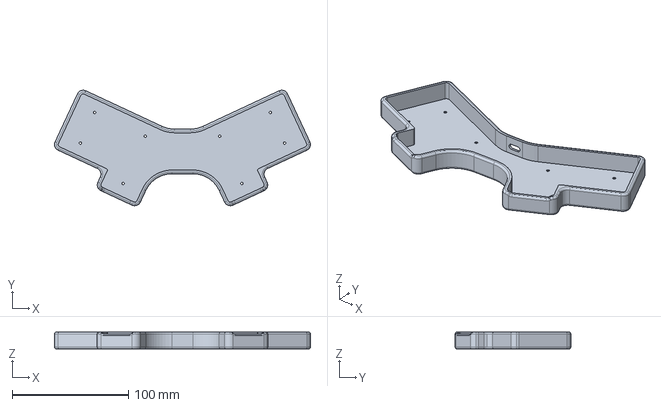
[picture p69: CAD file, 2026-02-12]
ScottoRang/PCB/Case/ScottoRang (PCB Edition) - Case.step
220.2 x 99.4 x 14.6 mm
