joe-scotto/scottokeebs/ScottoSlant/Handwired/Case/ScottoSlant - Plate.step

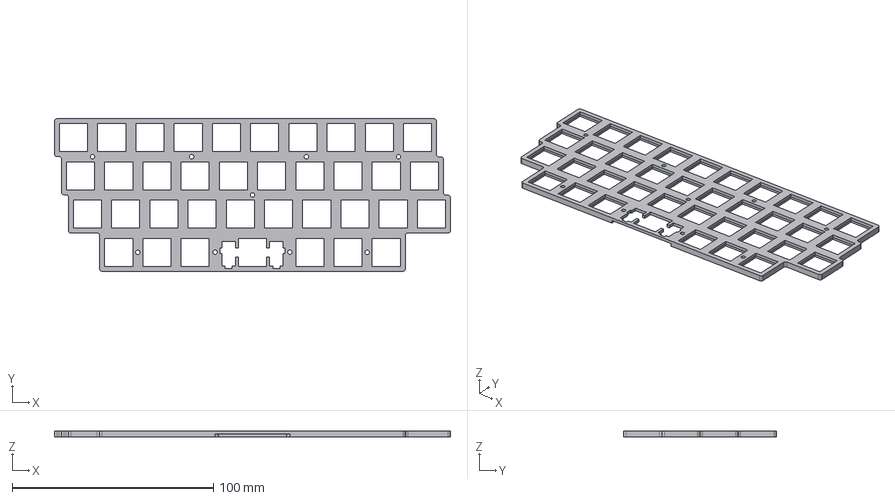
[picture p70: CAD file, 2023-06-10]
ScottoSlant/Handwired/Case/ScottoSlant - Plate.step
196.8 x 75.9 x 3.00 mm
