joe-scotto/scottokeebs/ScottoSlant/PCB/Case/ScottoSlant (PCB Edition) - Cover.step

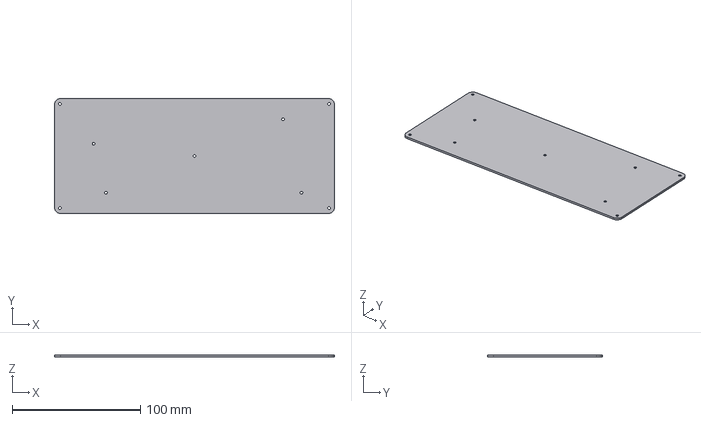
[picture p71: CAD file, 2024-09-14]
ScottoSlant/PCB/Case/ScottoSlant (PCB Edition) - Cover.step
218.3 x 89.7 x 1.60 mm
