joe-scotto/scottokeebs/ScottoSplit/Case/ScottoSplit - 3x6 - Case (Left).step

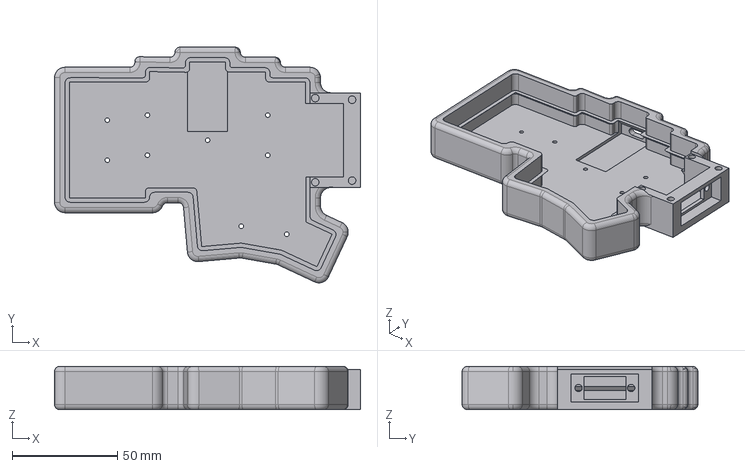
[picture p72: CAD file, 2023-11-27]
ScottoSplit/Case/ScottoSplit - 3x6 - Case (Left).step
145.4 x 111.9 x 20.6 mm
