joe-scotto/scottokeebs/ScottoStarter/Case/ScottoStarter - Keycaps (Flat).3mf

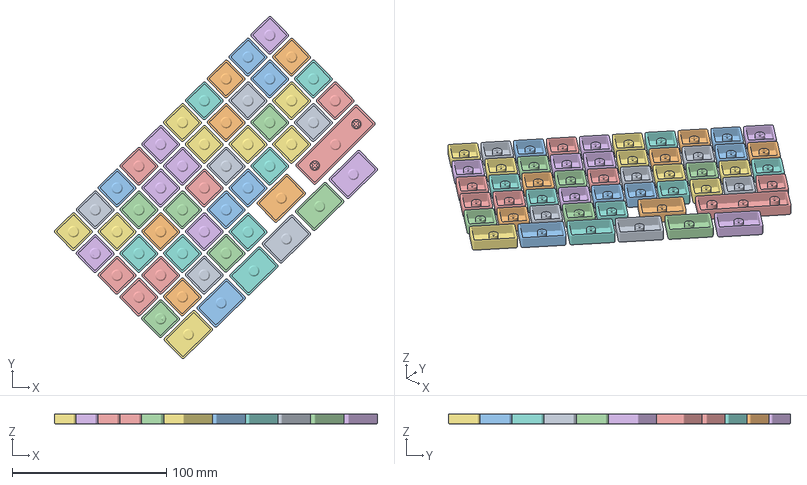
[picture p73: CAD file, 2026-08-09]
ScottoStarter/Case/ScottoStarter - Keycaps (Flat).3mf
209.4 x 221.8 x 6.70 mm
Right_Text
Down_Keycap
K_Keycap
Left_Keycap
Question_Text
1_Keycap
T_Keycap
Less_Keycap
Left_Text
E_Keycap
R_Text
G_Text
Question_Keycap
6_Text
Semicolon_Text
Up_Text
J_Text
P_Text
Less_Text
Right_Keycap
Greater_Keycap
Backspace_Text
G_Keycap
M_Text
F_Keycap
K_Text
W_Keycap
5_Text
Z_Text
V_Text
C_Keycap
V_Keycap
X_Keycap
X_Text
B_Keycap
C_Text
Z_Keycap
M_Keycap
Greater_Text
Down_Text
Up_Keycap
0_Text
O_Text
7_Text
O_Keycap
Semicolon_Keycap
Y_Keycap
I_Keycap
I_Text
3_Keycap
E_Text
N_Keycap
H_Keycap
U_Text
Semicolon_Text_(2)
H_Text
D_Keycap
D_Text
T_Text
S_Keycap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
