joe-scotto/scottokeebs/ScottoT9/Handwired/Case/ScottoT9 - Plate.step

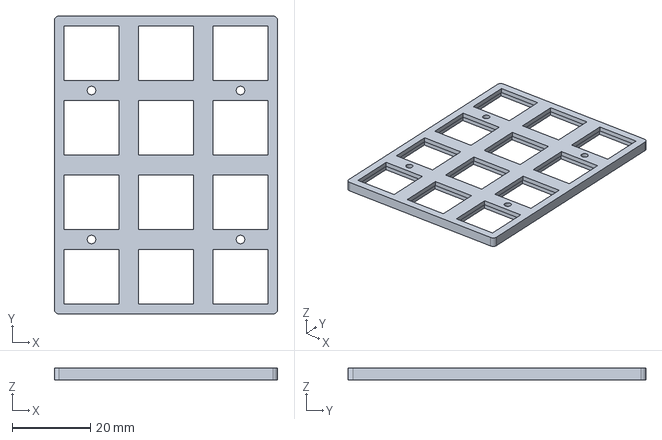
[picture p74: CAD file, 2025-11-11]
ScottoT9/Handwired/Case/ScottoT9 - Plate.step
57.1 x 76.2 x 3.00 mm
