joe-scotto/scottokeebs/ScottoT9/PCB/Case/ScottoT9 (PCB Edition) - Case.step

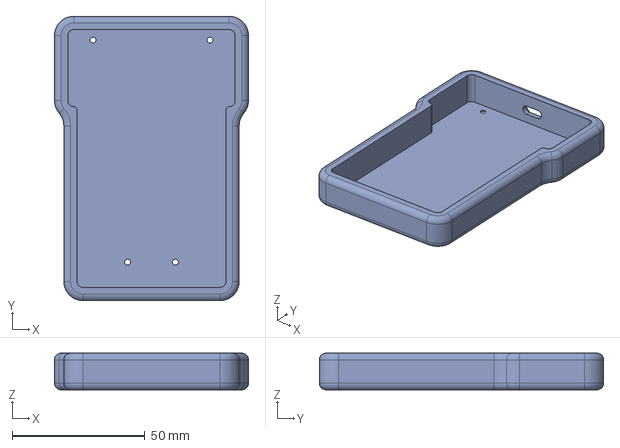
[picture p75: CAD file, 2025-12-09]
ScottoT9/PCB/Case/ScottoT9 (PCB Edition) - Case.step
73.0 x 107.0 x 13.8 mm
