joe-scotto/scottokeebs/ScottoWing/Handwired/Case/ScottoWing - 3x6 - Bottom (ScottoKeebs).step

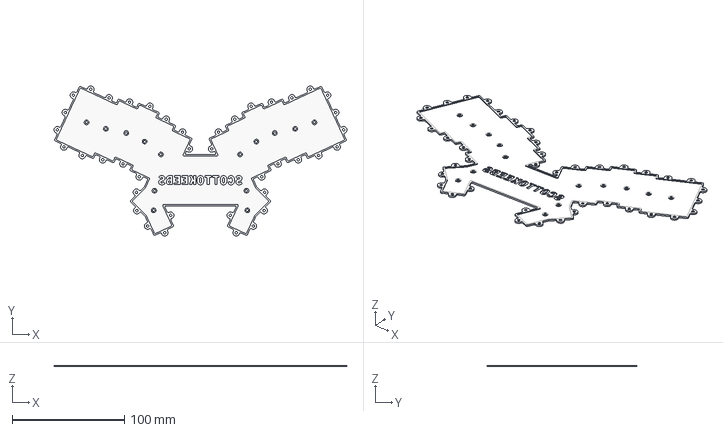
[picture p76: CAD file, 2023-11-20]
ScottoWing/Handwired/Case/ScottoWing - 3x6 - Bottom (ScottoKeebs).step
260.6 x 133.3 x 1.20 mm
