joe-scotto/scottokeebs/ScottoWing/PCB/Case/ScottoWing (PCB Edition) - 3x6.step

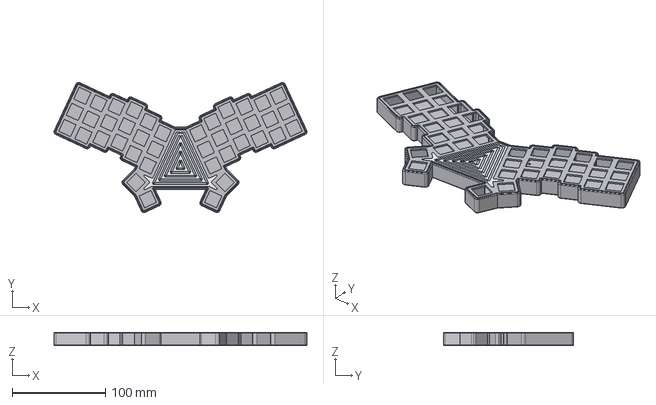
[picture p77: CAD file, 2024-06-28]
ScottoWing/PCB/Case/ScottoWing (PCB Edition) - 3x6.step
271.6 x 139.7 x 14.4 mm
