joe-scotto/scottokeebs/Extras/ScottoBender/ScottoBender - Middle.step

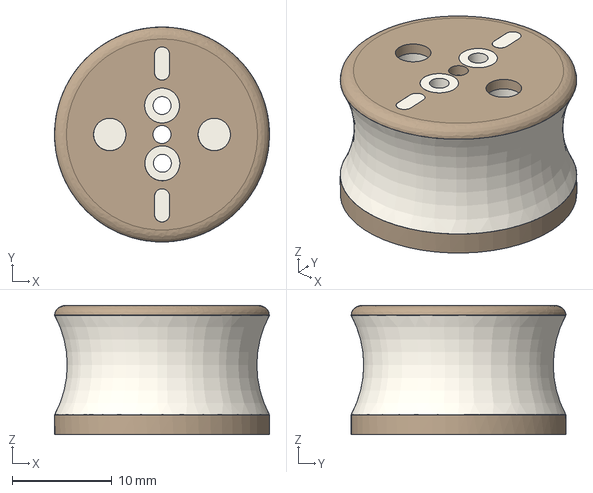
[picture p78: CAD file, 2024-01-28]
Extras/ScottoBender/ScottoBender - Middle.step
21.6 x 21.6 x 13.0 mm
