joe-scotto/scottokeebs/Extras/ScottoBender/V1/ScottoBender - ScottoBender (18g).step

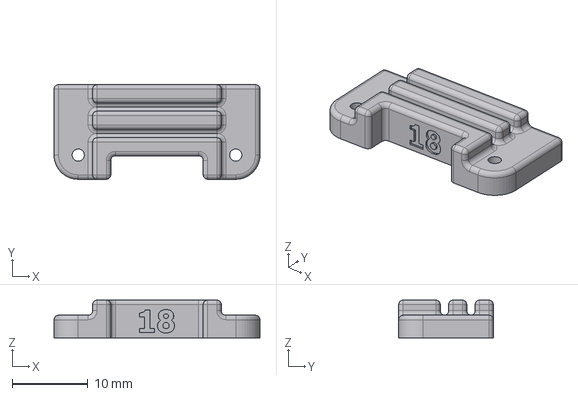
[picture p79: CAD file, 2023-08-27]
Extras/ScottoBender/V1/ScottoBender - ScottoBender (18g).step
27.2 x 12.5 x 5.00 mm
