joe-scotto/scottokeebs/Extras/ScottoCaps/Flat/Blanks/2.75u.step

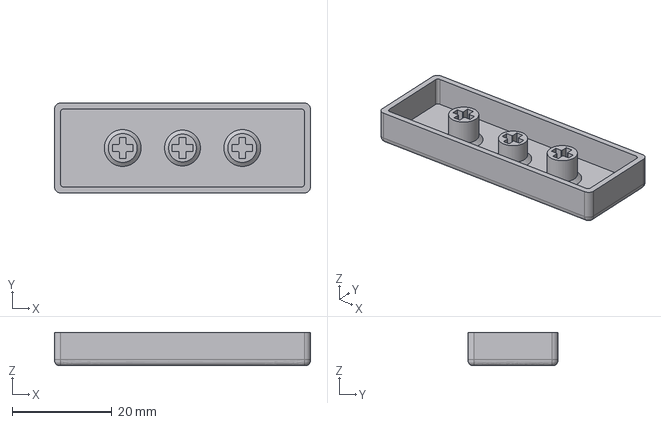
[picture p80: CAD file, 2024-02-25]
Extras/ScottoCaps/Flat/Blanks/2.75u.step
51.4 x 18.0 x 6.70 mm
