joe-scotto/scottokeebs/Extras/ScottoCaps/Glass/Choc/ScottoCaps (Glass) - 1.75u.stl

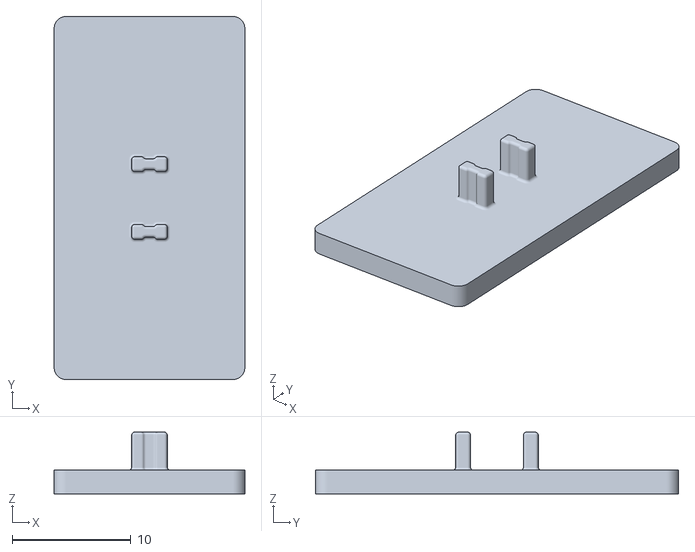
[picture p81: CAD file, 2023-08-21]
Extras/ScottoCaps/Glass/Choc/ScottoCaps (Glass) - 1.75u.stl
16.0 x 30.5 x 5.20
