joe-scotto/scottokeebs/Extras/ScottoCaps/Glass/MX/ScottoCaps (Glass) - 2.00u.step

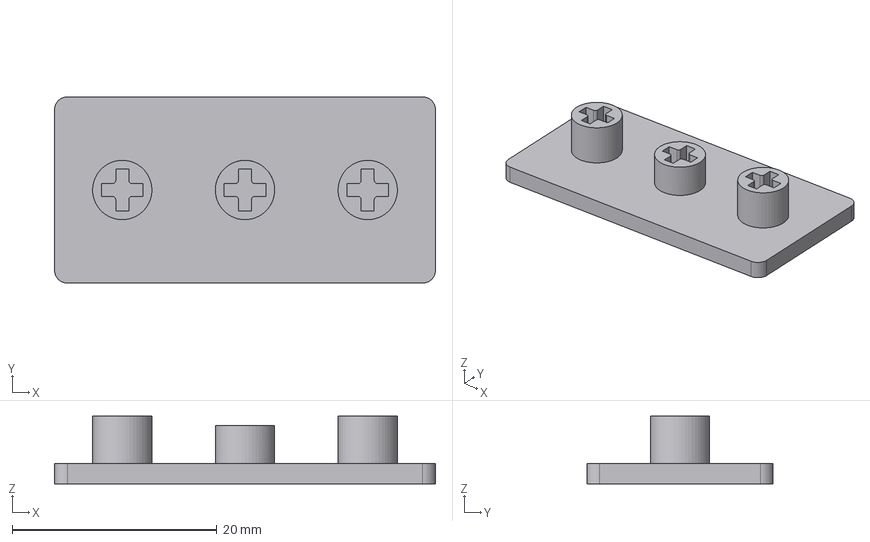
[picture p82: CAD file, 2023-08-16]
Extras/ScottoCaps/Glass/MX/ScottoCaps (Glass) - 2.00u.step
37.2 x 18.2 x 6.60 mm
