joe-scotto/scottokeebs/Extras/ScottoCaps/Scooped/Choc/Blanks/16x16/1.00u (16x16 - Homing - Concave).step

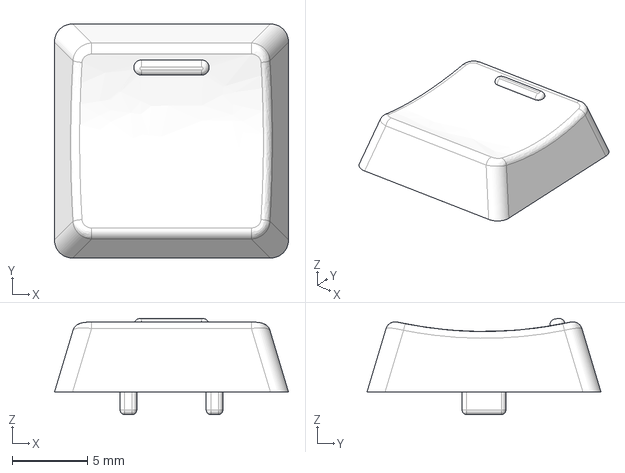
[picture p83: CAD file, 2025-04-24]
Extras/ScottoCaps/Scooped/Choc/Blanks/16x16/1.00u (16x16 - Homing - Concave).step
15.5 x 15.5 x 6.37 mm
