joe-scotto/scottokeebs/Extras/ScottoCaps/Scooped/Choc/Blanks/18x17/1.50u (18x17 - Concave).step

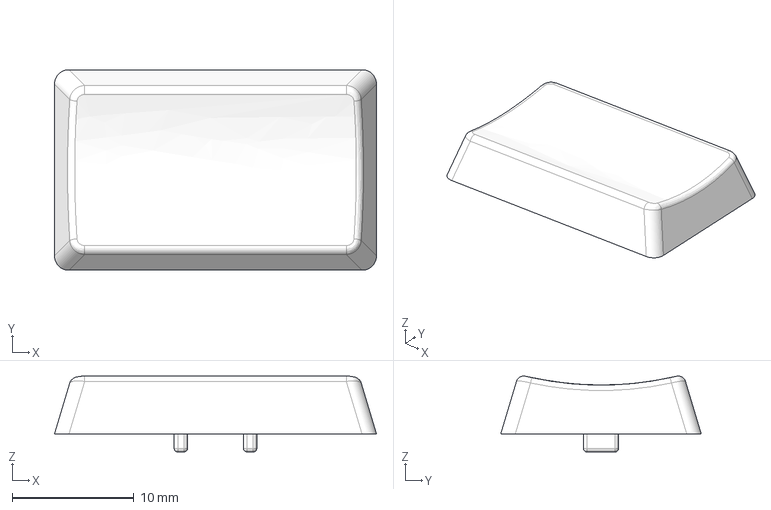
[picture p84: CAD file, 2025-04-24]
Extras/ScottoCaps/Scooped/Choc/Blanks/18x17/1.50u (18x17 - Concave).step
26.5 x 16.5 x 6.25 mm
