joe-scotto/scottokeebs/Extras/ScottoCaps/Scooped/Choc/Blanks/18x18/1.00u (18x18 - Convex).step

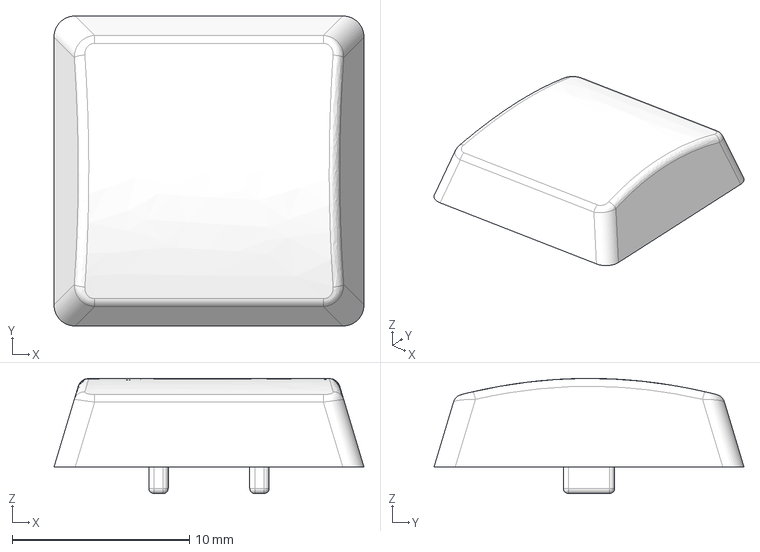
[picture p85: CAD file, 2025-04-24]
Extras/ScottoCaps/Scooped/Choc/Blanks/18x18/1.00u (18x18 - Convex).step
17.5 x 17.5 x 6.50 mm
