joe-scotto/scottokeebs/Extras/ScottoCaps/Scooped/Choc/Legends/16x16/5 (16x16).3mf

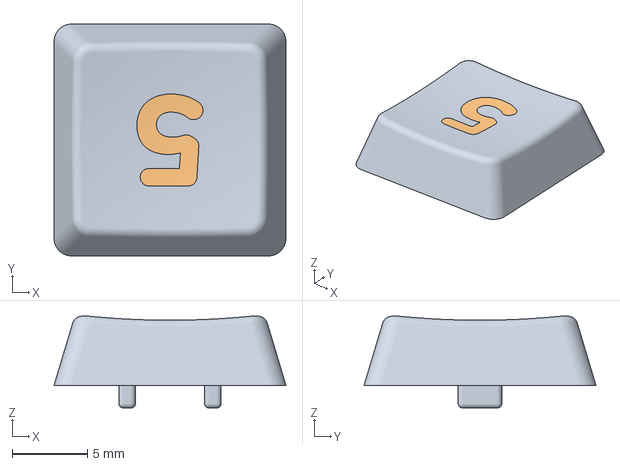
[picture p86: CAD file, 2025-04-24]
Extras/ScottoCaps/Scooped/Choc/Legends/16x16/5 (16x16).3mf
15.4 x 15.4 x 6.11 mm
Keycap
Legend
