joe-scotto/scottokeebs/Extras/ScottoCaps/Scooped/MX/Blanks/2x2 POS (Concave).step

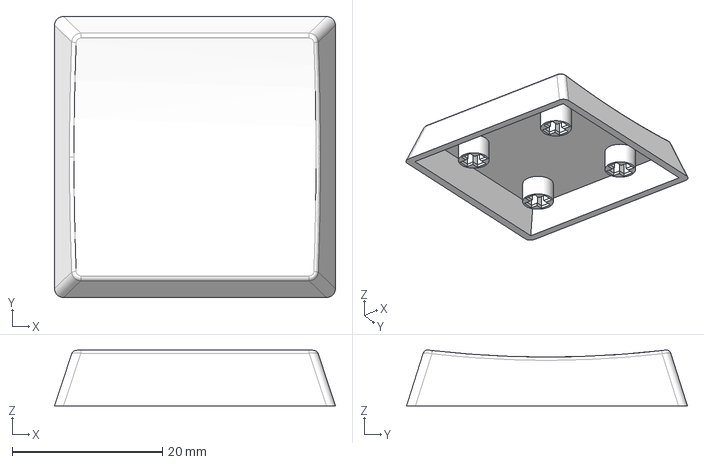
[picture p87: CAD file, 2023-12-27]
Extras/ScottoCaps/Scooped/MX/Blanks/2x2 POS (Concave).step
37.4 x 37.3 x 7.44 mm
