joe-scotto/scottokeebs/Extras/ScottoCaps/Scooped/MX/Raw/2.25u (Raw).step

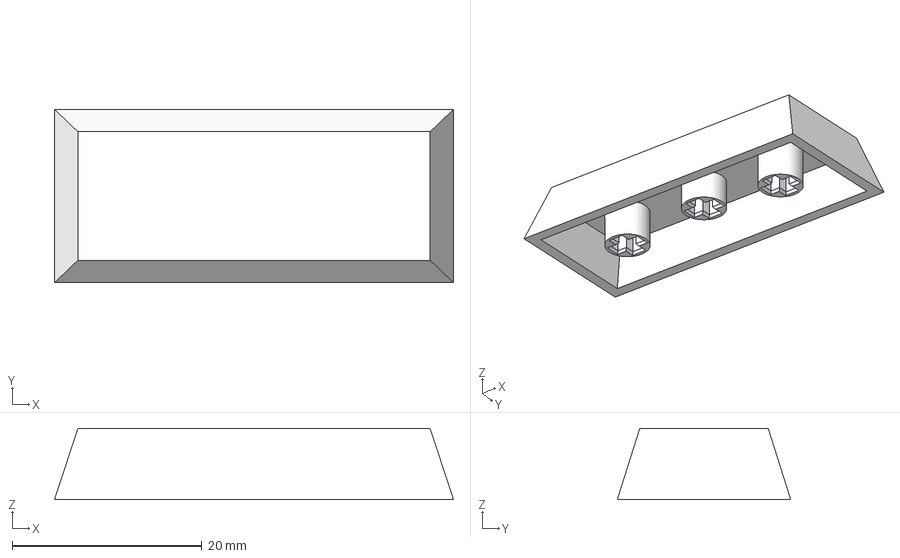
[picture p88: CAD file, 2026-04-09]
Extras/ScottoCaps/Scooped/MX/Raw/2.25u (Raw).step
42.1 x 18.3 x 7.50 mm
