joe-scotto/scottokeebs/Extras/ScottoCaps/Sculpted/Blanks/R3 - 3.00u (Flat).step

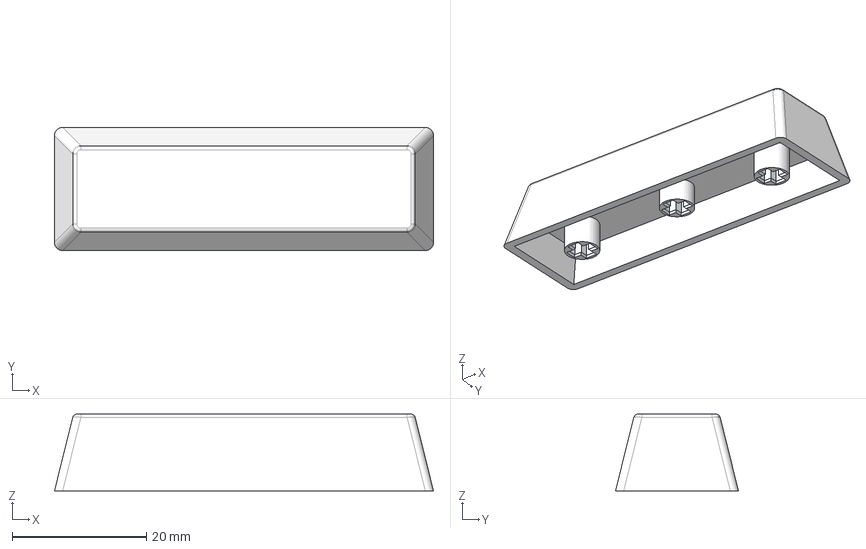
[picture p89: CAD file, 2025-02-17]
Extras/ScottoCaps/Sculpted/Blanks/R3 - 3.00u (Flat).step
56.4 x 18.3 x 11.4 mm
