joe-scotto/scottokeebs/Extras/ScottoCaps/Standard/ScottoCaps (Standard) - 2.25u.step

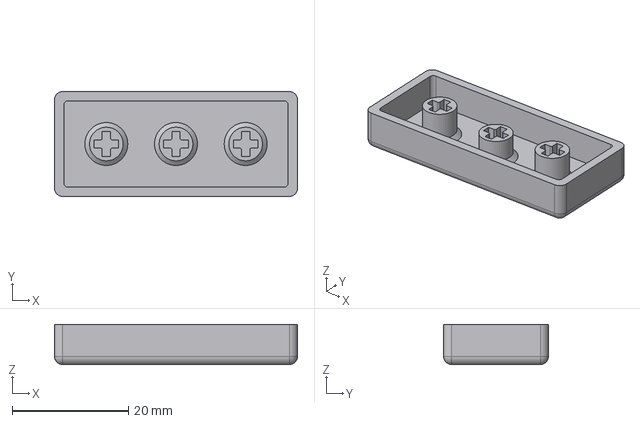
[picture p90: CAD file, 2023-10-19]
Extras/ScottoCaps/Standard/ScottoCaps (Standard) - 2.25u.step
41.9 x 18.0 x 6.90 mm
