joe-scotto/scottokeebs/Extras/ScottoCoiler/Bambu.3mf

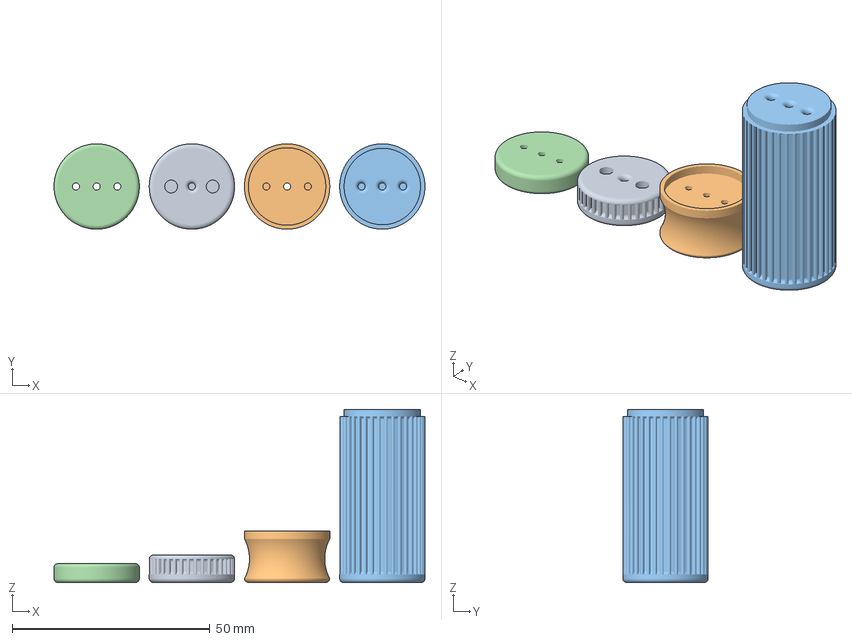
[picture p91: CAD file, 2024-01-28]
Extras/ScottoCoiler/Bambu.3mf
93.9 x 21.6 x 43.8 mm
ScottoCoiler - Top (Symbol)
ScottoCoiler - Middle
ScottoCoiler - Bottom
Cutter
