joe-scotto/scottokeebs/Extras/ScottoHousing/ScottoHousing - USB-A Sizer.step

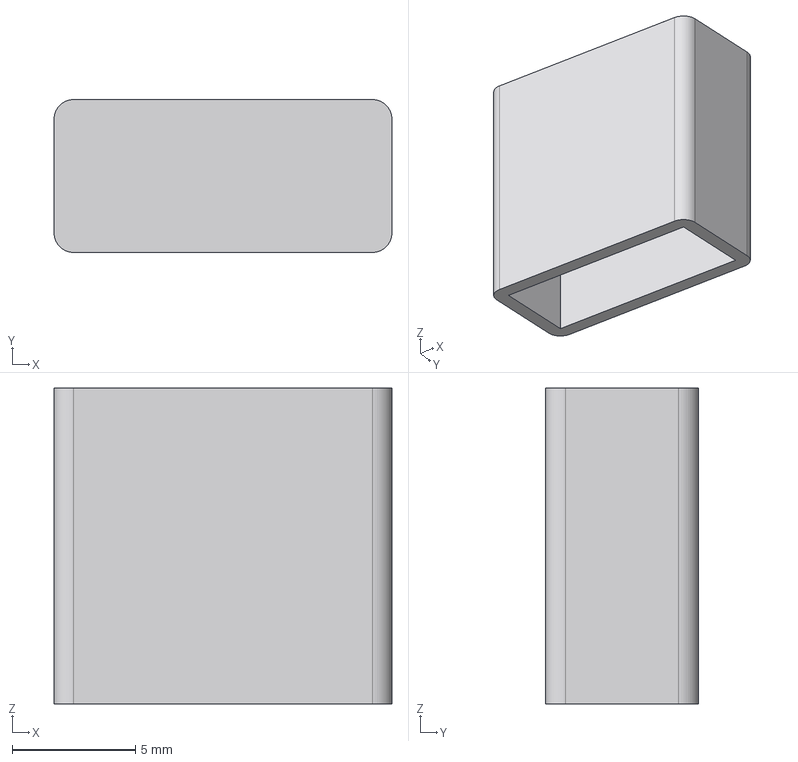
[picture p92: CAD file, 2025-08-10]
Extras/ScottoHousing/ScottoHousing - USB-A Sizer.step
13.7 x 6.20 x 12.8 mm
