joe-scotto/scottokeebs/Extras/ScottoShrink/ScottoShrink - Base.step

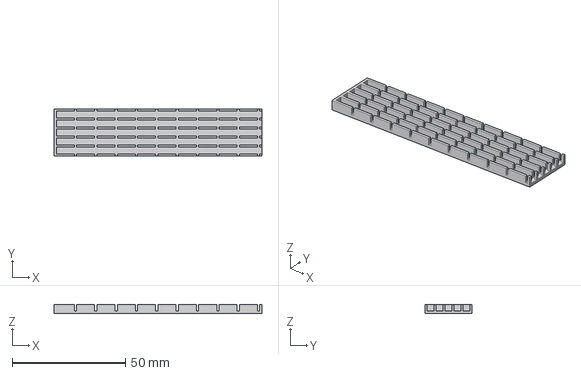
[picture p93: CAD file, 2025-12-25]
Extras/ScottoShrink/ScottoShrink - Base.step
92.0 x 21.0 x 4.20 mm
