joe-scotto/scottokeebs/Scotto108/Case/Scotto108 - Plate (Middle).step

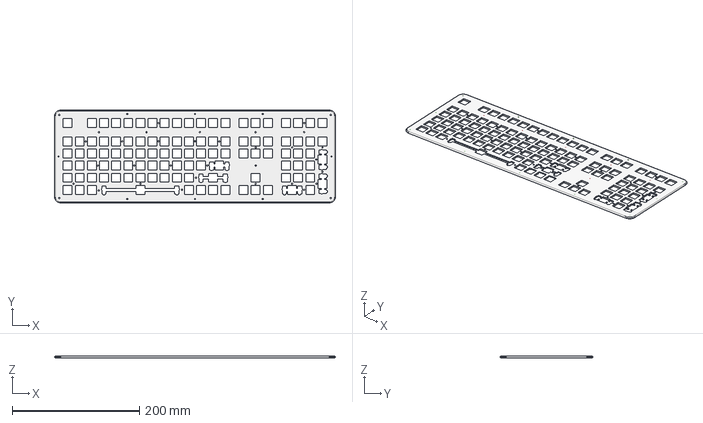
[picture p94: CAD file, 2026-04-20]
Scotto108/Case/Scotto108 - Plate (Middle).step
441.1 x 145.8 x 3.00 mm
