joe-scotto/scottokeebs/Scotto16/Case/Scotto16 - Case.step

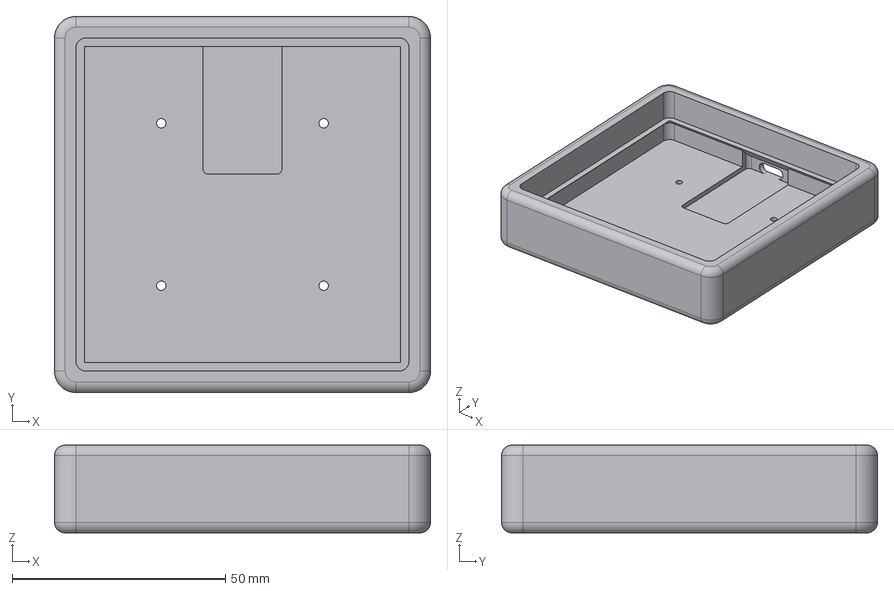
[picture p95: CAD file, 2025-05-08]
Scotto16/Case/Scotto16 - Case.step
88.2 x 88.2 x 20.6 mm
