joe-scotto/scottokeebs/Scotto2/Case/Scotto2 - Bottom.step

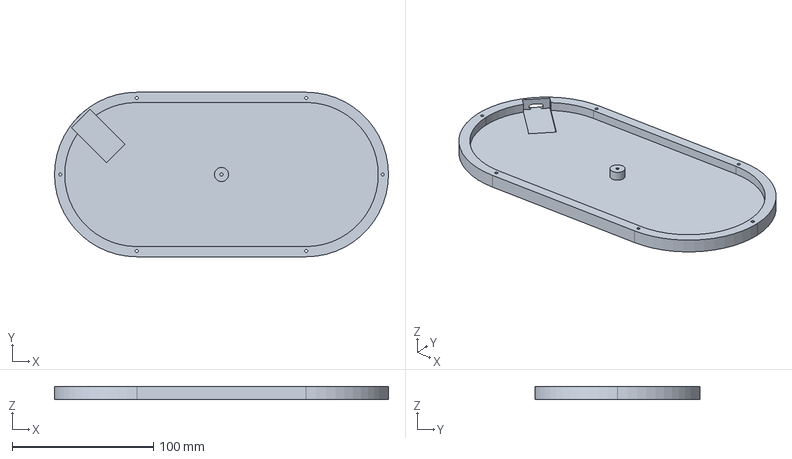
[picture p96: CAD file, 2026-05-15]
Scotto2/Case/Scotto2 - Bottom.step
236.5 x 116.5 x 9.00 mm
