joe-scotto/scottokeebs/Scotto20/Case/Scotto20 - Plate.step

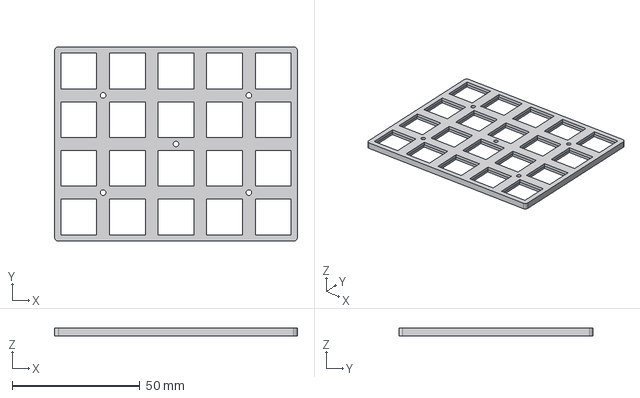
[picture p97: CAD file, 2025-07-22]
Scotto20/Case/Scotto20 - Plate.step
95.2 x 76.2 x 3.00 mm
