joe-scotto/scottokeebs/Scotto26/Case/Scotto26 - Case.step

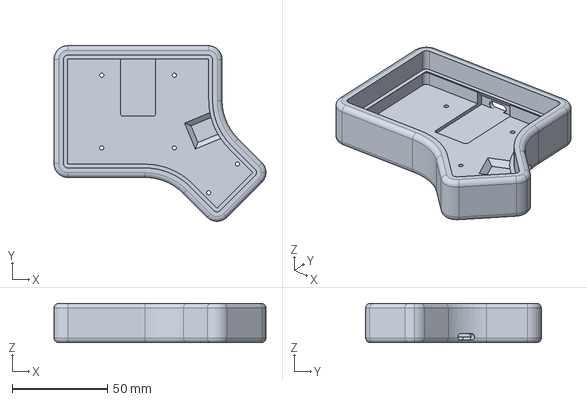
[picture p98: CAD file, 2026-09-21]
Scotto26/Case/Scotto26 - Case.step
111.3 x 92.2 x 20.6 mm
