joe-scotto/scottokeebs/Scotto34/Handwired/Case/Scotto34 - Case (V2).step

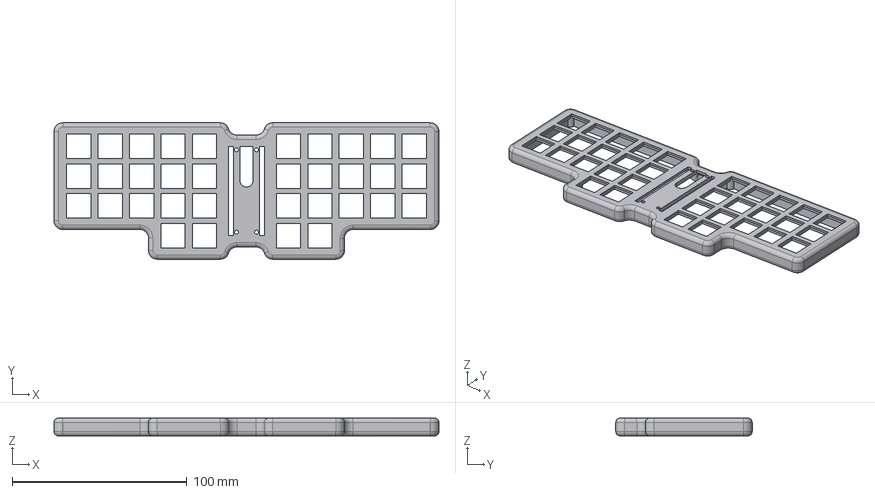
[picture p99: CAD file, 2025-06-09]
Scotto34/Handwired/Case/Scotto34 - Case (V2).step
220.0 x 78.0 x 10.2 mm
