joe-scotto/scottokeebs/Scotto34/PCB/Case/Keycaps/Choc V2 - 1.00u (Convex).step

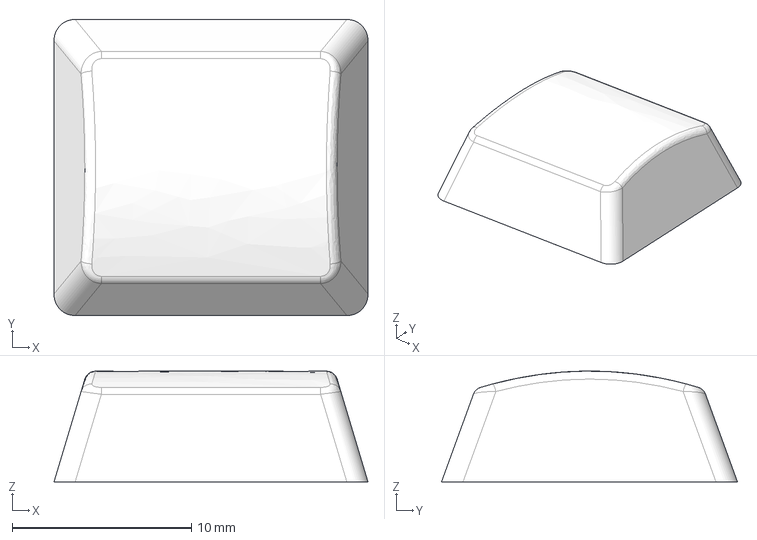
[picture p100: CAD file, 2026-10-05]
Scotto34/PCB/Case/Keycaps/Choc V2 - 1.00u (Convex).step
17.5 x 16.5 x 6.18 mm
