joe-scotto/scottokeebs/Scotto34/PCB/Case/Scotto34 (PCB Edition) - Plate (V2.0.0).step

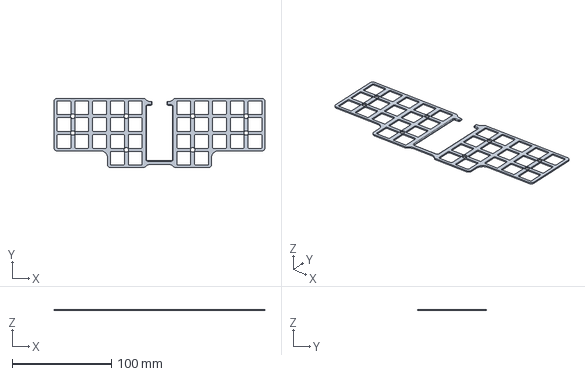
[picture p101: CAD file, 2026-10-05]
Scotto34/PCB/Case/Scotto34 (PCB Edition) - Plate (V2.0.0).step
213.0 x 70.0 x 1.20 mm
