joe-scotto/scottokeebs/Scotto36/Case/Scotto36 - Case.step

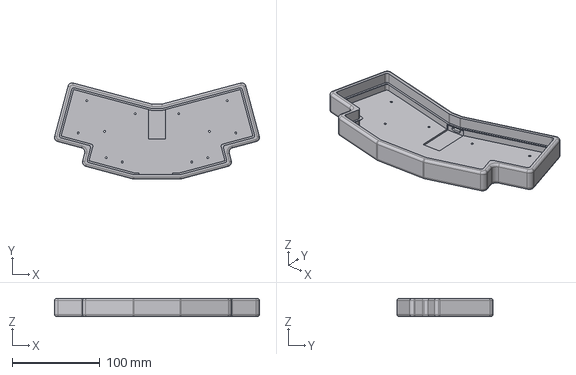
[picture p102: CAD file, 2023-06-10]
Scotto36/Case/Scotto36 - Case.step
233.4 x 109.5 x 20.6 mm
