joe-scotto/scottokeebs/Scotto37/Case/Scotto37 - Top (4mm Gasket).step

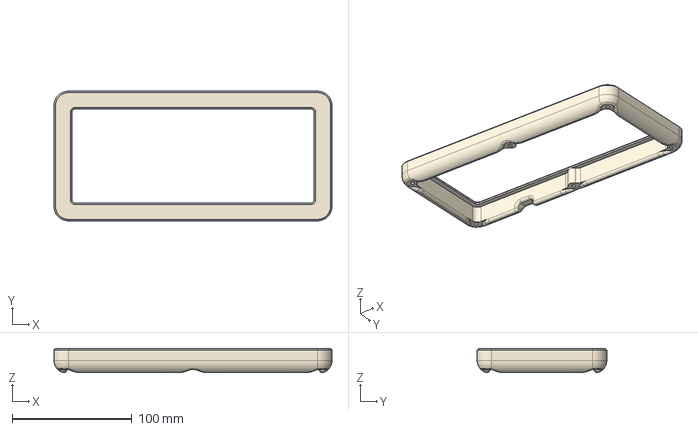
[picture p103: CAD file, 2024-06-03]
Scotto37/Case/Scotto37 - Top (4mm Gasket).step
232.0 x 108.2 x 20.3 mm
