joe-scotto/scottokeebs/Scotto40/Case/Scotto40 - Plate (2x2).step

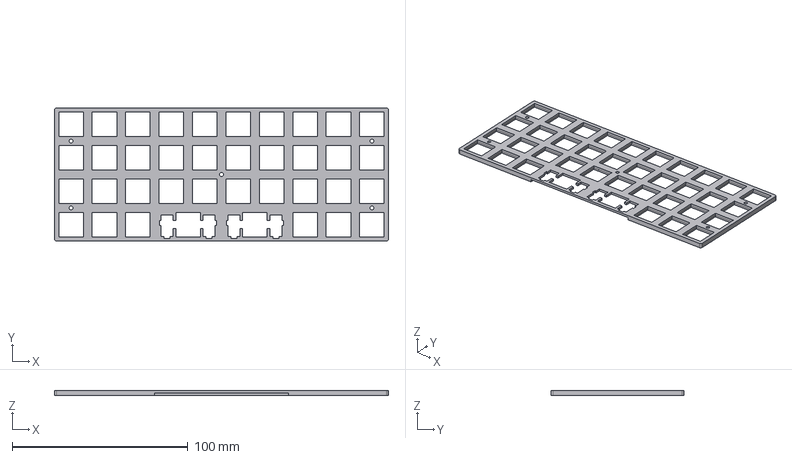
[picture p104: CAD file, 2025-12-25]
Scotto40/Case/Scotto40 - Plate (2x2).step
189.8 x 75.8 x 3.00 mm
