joe-scotto/scottokeebs/Scotto44/Case/Scotto44 - Plate (3x6).step

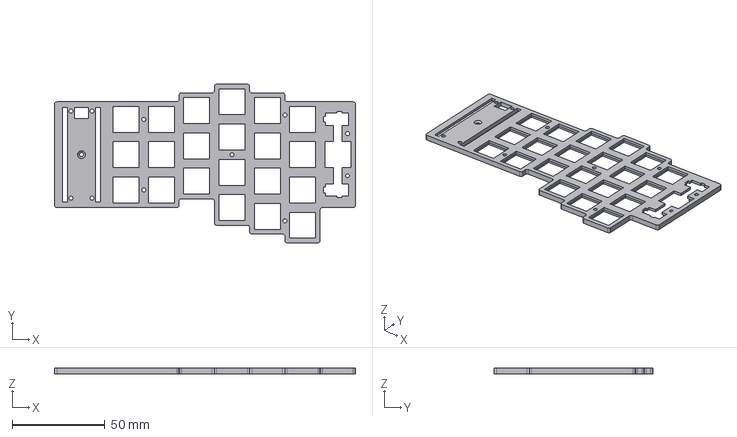
[picture p105: CAD file, 2024-12-22]
Scotto44/Case/Scotto44 - Plate (3x6).step
162.5 x 85.7 x 3.00 mm
