joe-scotto/scottokeebs/Scotto48/PCB/Case/Scotto48 (PCB Edition) - Plate.step

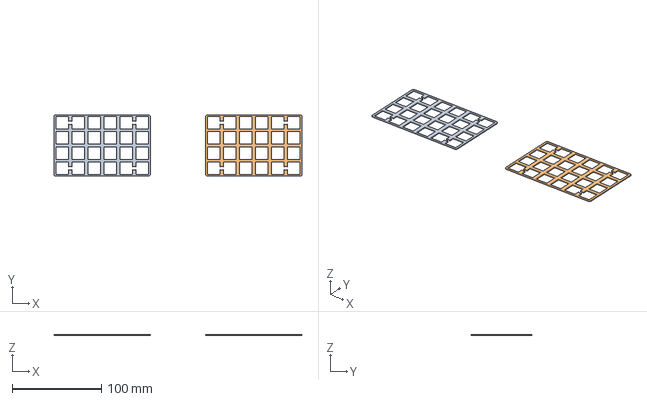
[picture p106: CAD file, 2026-06-23]
Scotto48/PCB/Case/Scotto48 (PCB Edition) - Plate.step
278.0 x 68.0 x 1.20 mm
