joe-scotto/scottokeebs/Scotto55/Case/Scotto55 - Top (ScottoKeebs).step

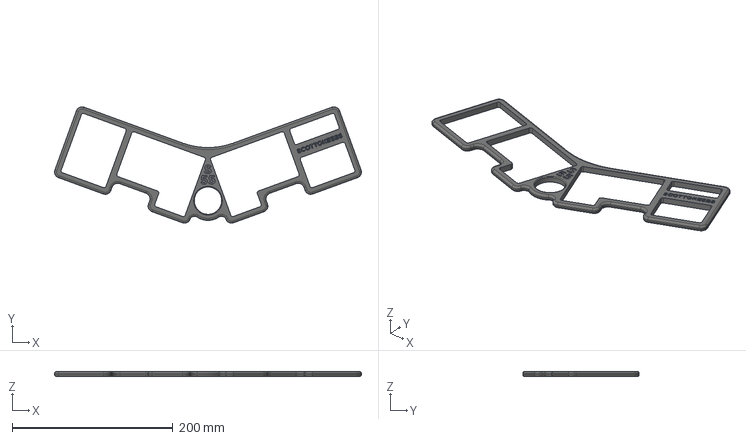
[picture p107: CAD file, 2026-03-06]
Scotto55/Case/Scotto55 - Top (ScottoKeebs).step
381.6 x 144.6 x 6.60 mm
