joe-scotto/scottokeebs/Scotto61/Case/Scotto61 - Case (Top).step

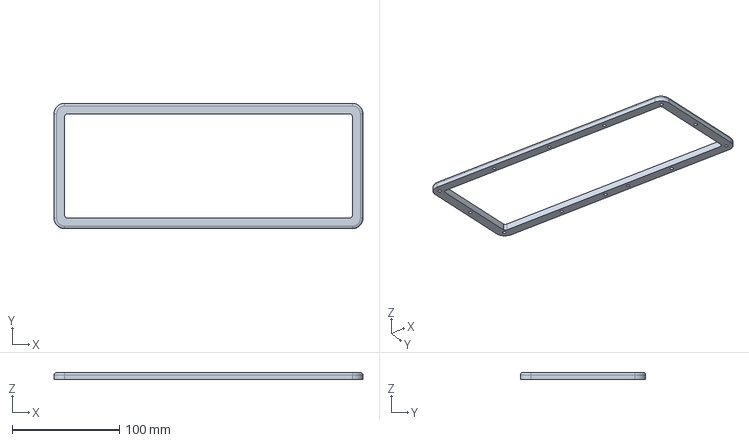
[picture p108: CAD file, 2023-12-15]
Scotto61/Case/Scotto61 - Case (Top).step
288.7 x 117.2 x 6.60 mm
