joe-scotto/scottokeebs/Scotto63/Case/Scotto63 - Cover (Blank - Tall).step

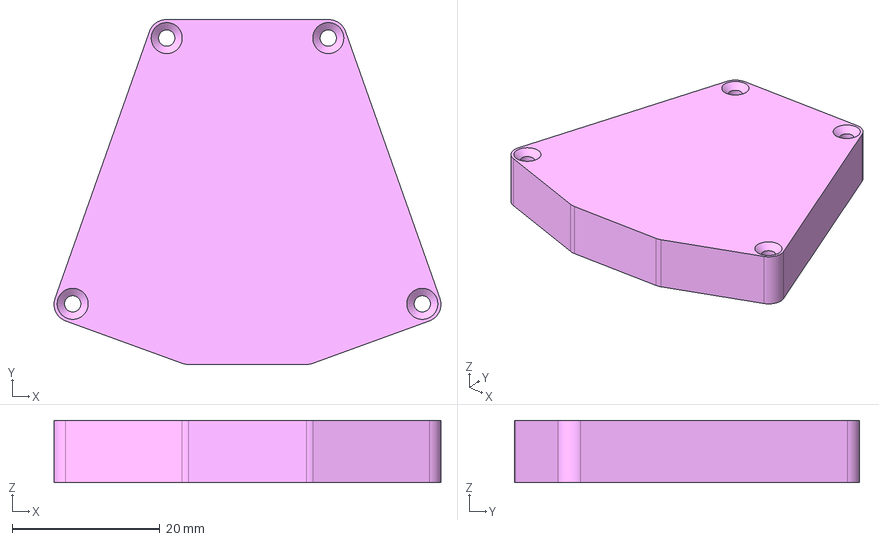
[picture p109: CAD file, 2024-02-19]
Scotto63/Case/Scotto63 - Cover (Blank - Tall).step
52.3 x 46.6 x 8.40 mm
