joe-scotto/scottokeebs/Scotto69/PCB/Case/Scotto69 (PCB Edition) - Case (Top).step

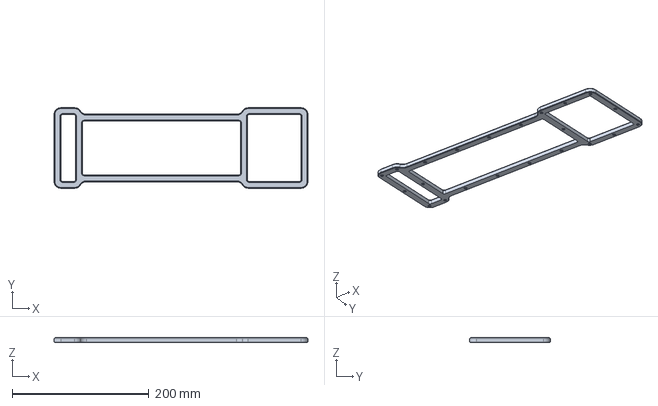
[picture p110: CAD file, 2025-03-08]
Scotto69/PCB/Case/Scotto69 (PCB Edition) - Case (Top).step
371.4 x 117.8 x 6.70 mm
