joe-scotto/scottokeebs/Scotto9/Case/Scotto9 - Case (RP2040 Pro Micro).step

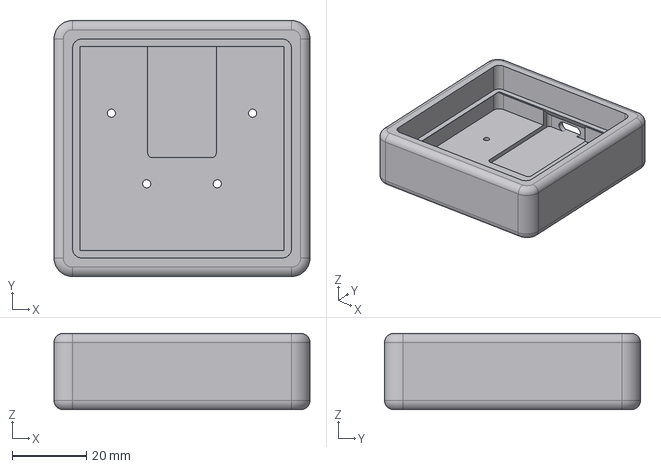
[picture p111: CAD file, 2026-04-25]
Scotto9/Case/Scotto9 - Case (RP2040 Pro Micro).step
69.1 x 69.1 x 20.6 mm
