joe-scotto/scottokeebs/ScottoAlp/Case/ScottoAlp - Plate (4x12_7).step

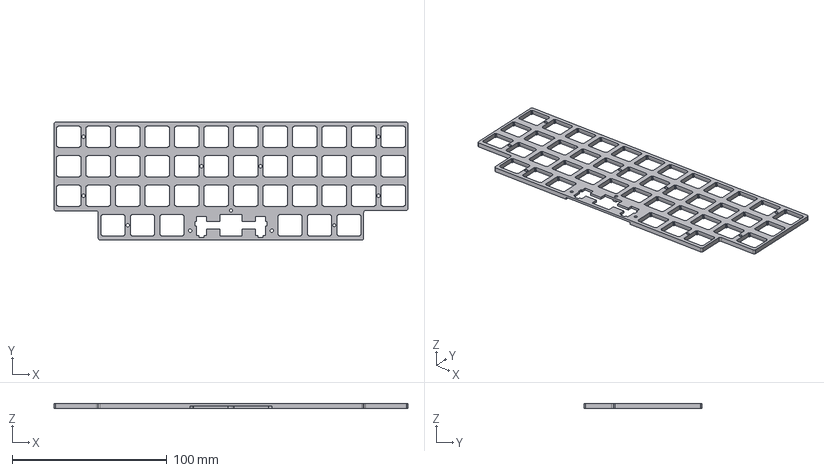
[picture p112: CAD file, 2023-12-31]
ScottoAlp/Case/ScottoAlp - Plate (4x12_7).step
228.6 x 76.2 x 3.00 mm
