joe-scotto/scottokeebs/ScottoBigum/Case/ScottoBigum - Case.step

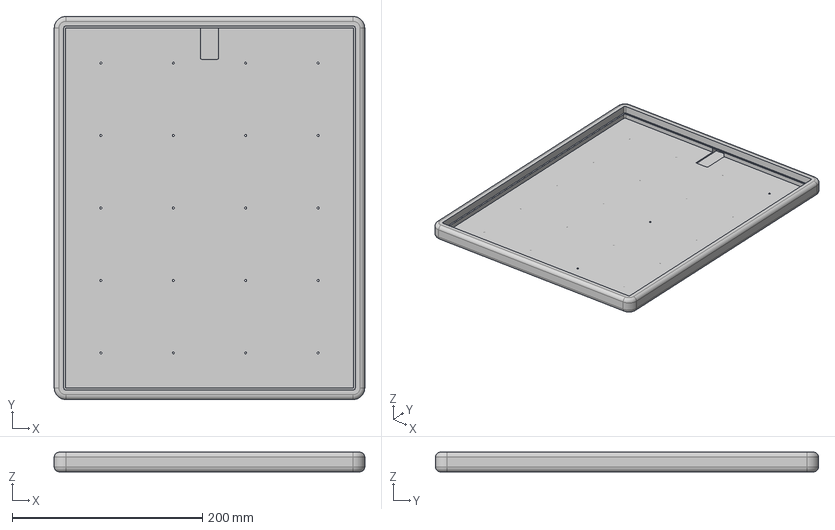
[picture p113: CAD file, 2026-07-09]
ScottoBigum/Case/ScottoBigum - Case.step
326.8 x 403.0 x 20.6 mm
