joe-scotto/scottokeebs/ScottoChoczard/Case/ScottoChoczard - Case.step

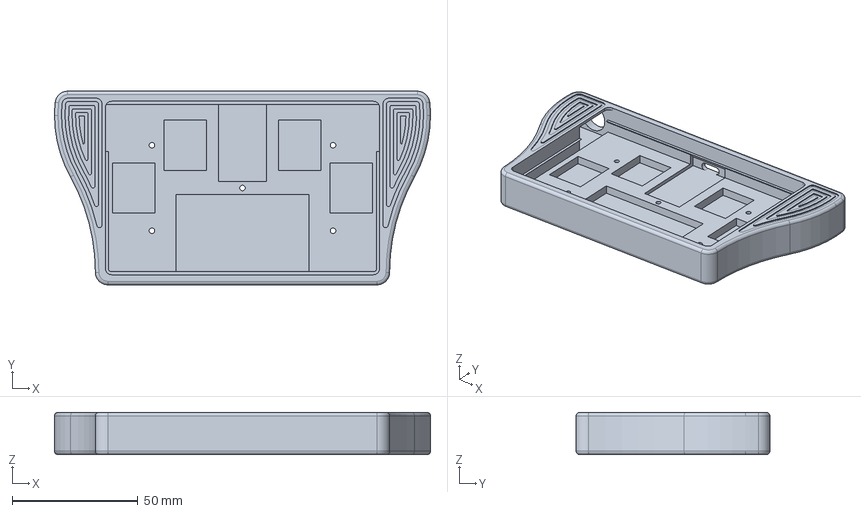
[picture p114: CAD file, 2024-10-28]
ScottoChoczard/Case/ScottoChoczard - Case.step
149.5 x 77.0 x 16.8 mm
