joe-scotto/scottokeebs/ScottoCirque/Case/ScottoCirque - Bottom.step

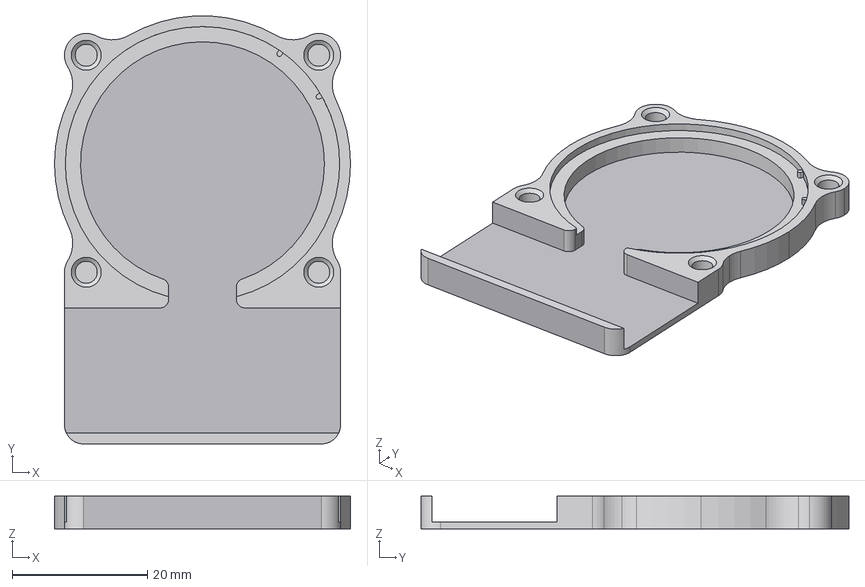
[picture p115: CAD file, 2026-08-07]
ScottoCirque/Case/ScottoCirque - Bottom.step
43.7 x 63.2 x 4.80 mm
