joe-scotto/scottokeebs/ScottoCMD/Case/ScottoCMD - Case.step

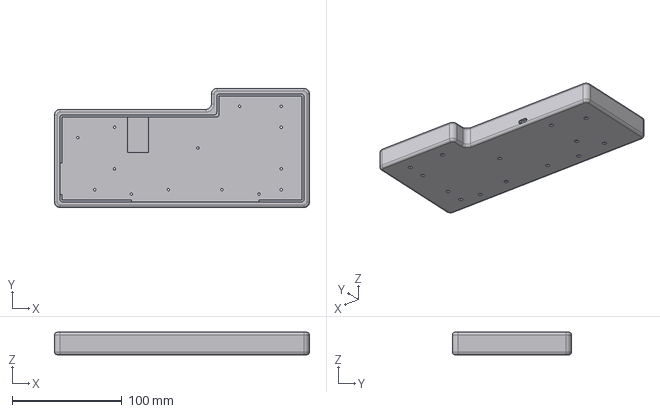
[picture p116: CAD file, 2023-06-13]
ScottoCMD/Case/ScottoCMD - Case.step
232.5 x 108.6 x 20.6 mm
