joe-scotto/scottokeebs/ScottoErgo/Case/ScottoErgo - Bottom.step

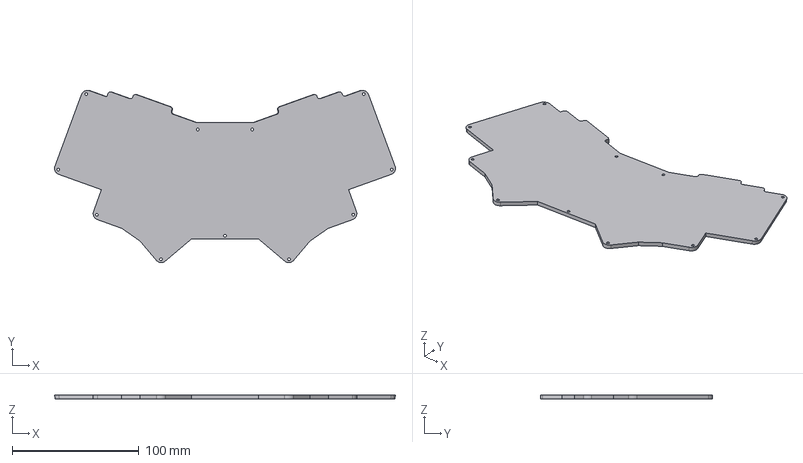
[picture p117: CAD file, 2023-06-14]
ScottoErgo/Case/ScottoErgo - Bottom.step
268.6 x 135.7 x 3.00 mm
