joe-scotto/scottokeebs/ScottoFly/Case/ScottoFly - Case.step

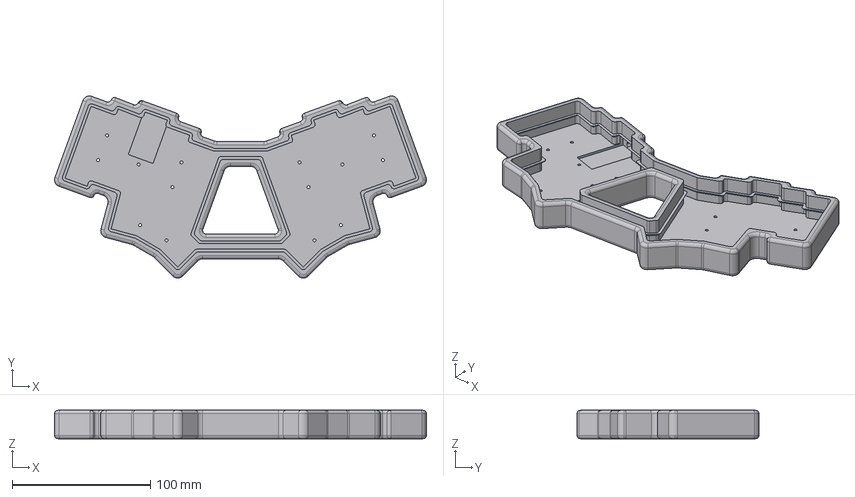
[picture p118: CAD file, 2023-06-14]
ScottoFly/Case/ScottoFly - Case.step
268.8 x 131.6 x 20.6 mm
