joe-scotto/scottokeebs/ScottoFrog/Case/ScottoFrog - Plate.step

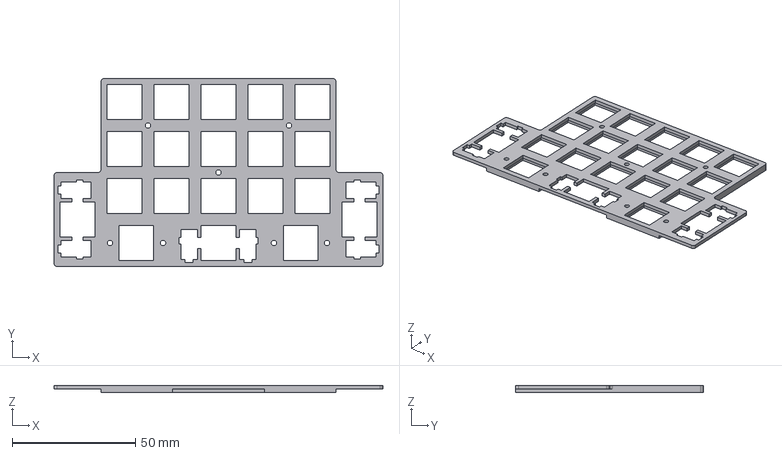
[picture p119: CAD file, 2023-06-12]
ScottoFrog/Case/ScottoFrog - Plate.step
133.3 x 76.2 x 3.00 mm
