joe-scotto/scottokeebs/ScottoFrog/Handwired/Case/ScottoFrog - Case (RP2040 Pro Micro) - CNC.step

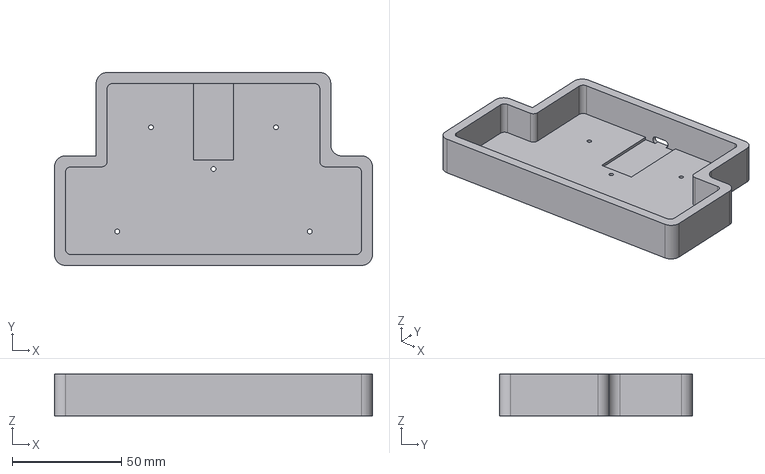
[picture p120: CAD file, 2025-04-22]
ScottoFrog/Handwired/Case/ScottoFrog - Case (RP2040 Pro Micro) - CNC.step
145.3 x 88.2 x 19.0 mm
