joe-scotto/scottokeebs/ScottoFrog/PCB/Case/ScottoFrog (PCB Edition) - Plate.step

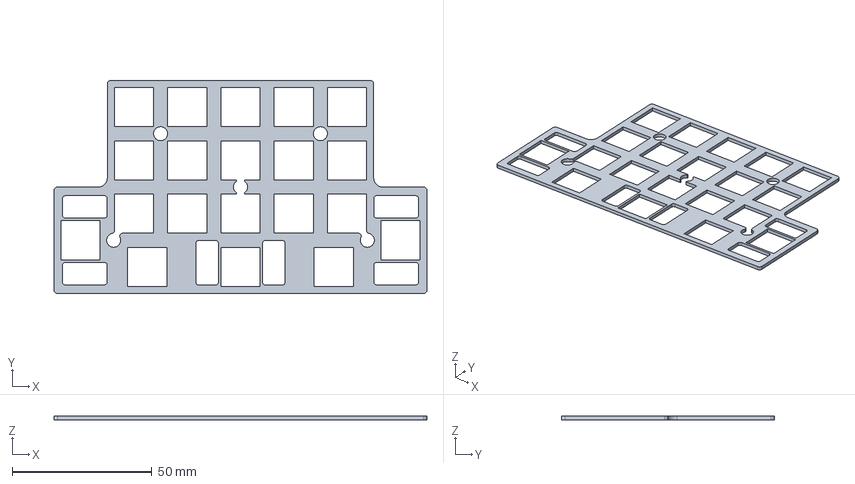
[picture p121: CAD file, 2025-11-27]
ScottoFrog/PCB/Case/ScottoFrog (PCB Edition) - Plate.step
133.3 x 76.2 x 1.40 mm
