joe-scotto/scottokeebs/ScottoGame/Case/ScottoGame - OLED (Frame).stl

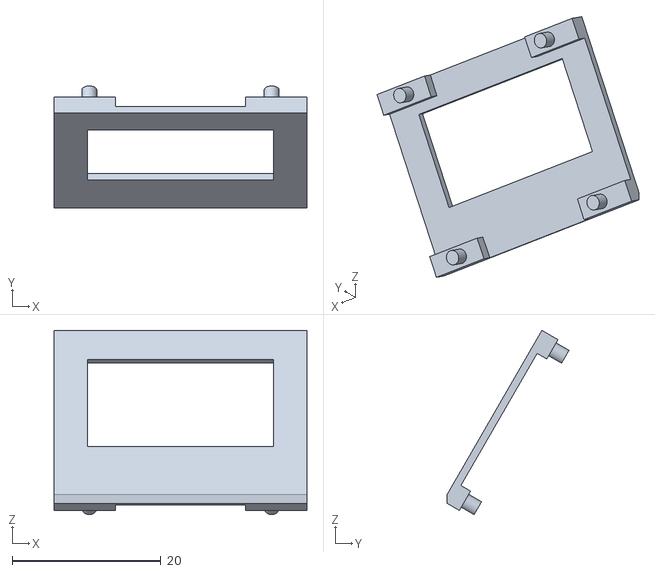
[picture p122: CAD file, 2023-06-12]
ScottoGame/Case/ScottoGame - OLED (Frame).stl
34.0 x 16.4 x 24.8
