joe-scotto/scottokeebs/ScottoInvader/Case/ScottoInvader - Case.step

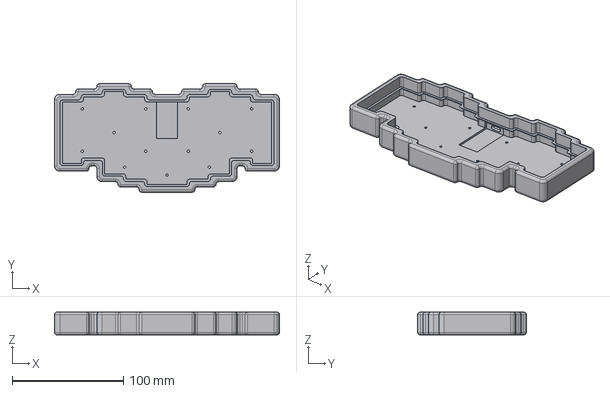
[picture p123: CAD file, 2023-06-10]
ScottoInvader/Case/ScottoInvader - Case.step
202.5 x 97.8 x 20.6 mm
