joe-scotto/scottokeebs/ScottoKatana/Handwired/Case/ScottoKatana - Gasket Plate (0.25mm Tolerance).step

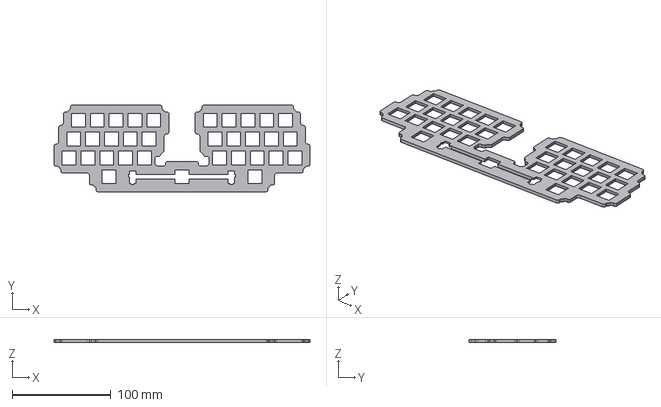
[picture p124: CAD file, 2024-01-03]
ScottoKatana/Handwired/Case/ScottoKatana - Gasket Plate (0.25mm Tolerance).step
259.1 x 87.7 x 3.00 mm
