joe-scotto/scottokeebs/ScottoLong/PCB/Case/ScottoLong (PCB Edition) - Case.step

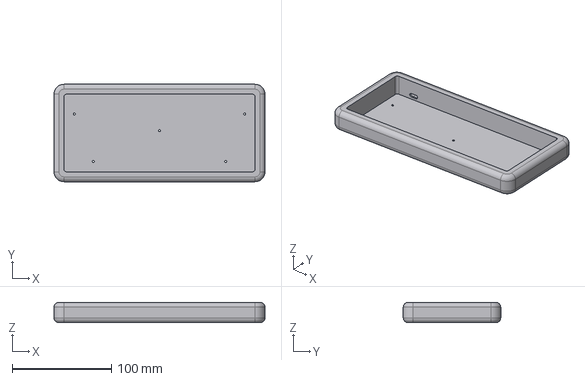
[picture p126: CAD file, 2024-07-18]
ScottoLong/PCB/Case/ScottoLong (PCB Edition) - Case.step
212.5 x 98.2 x 20.6 mm
