joe-scotto/scottokeebs/ScottoMacrodeck/Case/ScottoMacrodeck - Case.step

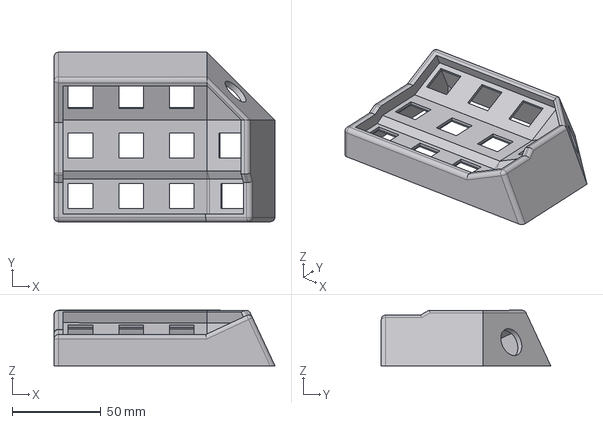
[picture p127: CAD file, 2023-06-10]
ScottoMacrodeck/Case/ScottoMacrodeck - Case.step
124.7 x 95.7 x 31.3 mm
