joe-scotto/scottokeebs/ScottoMouse/Case/ScottoMouse - Case (Black Pico).step

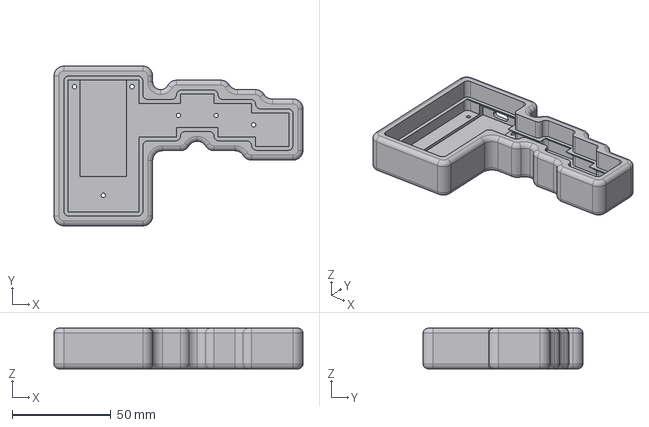
[picture p128: CAD file, 2023-06-10]
ScottoMouse/Case/ScottoMouse - Case (Black Pico).step
126.2 x 81.0 x 20.6 mm
