joe-scotto/scottokeebs/ScottoNum/Case/ScottoNum - Middle.step

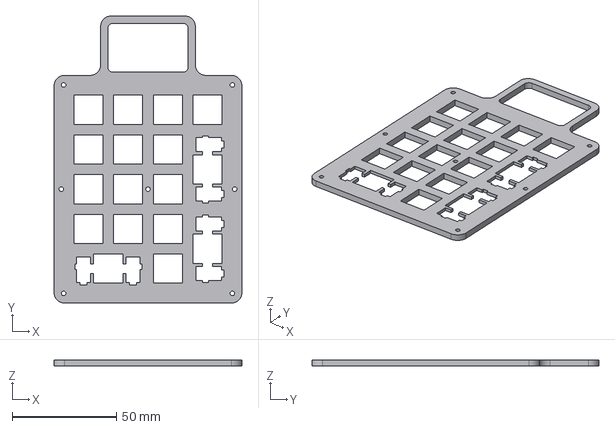
[picture p129: CAD file, 2023-06-11]
ScottoNum/Case/ScottoNum - Middle.step
90.2 x 137.7 x 3.00 mm
