joe-scotto/scottokeebs/ScottoPad/Case/ScottoPad - Plate.step

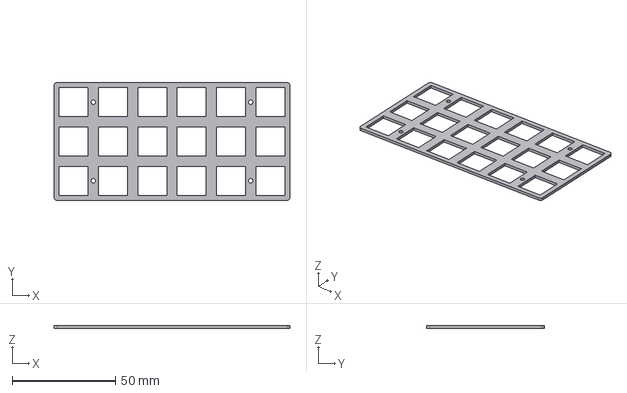
[picture p130: CAD file, 2025-04-05]
ScottoPad/Case/ScottoPad - Plate.step
114.3 x 57.1 x 1.40 mm
