joe-scotto/scottokeebs/ScottoRang/Handwired/Case/ScottoRang - OLED Cover.step

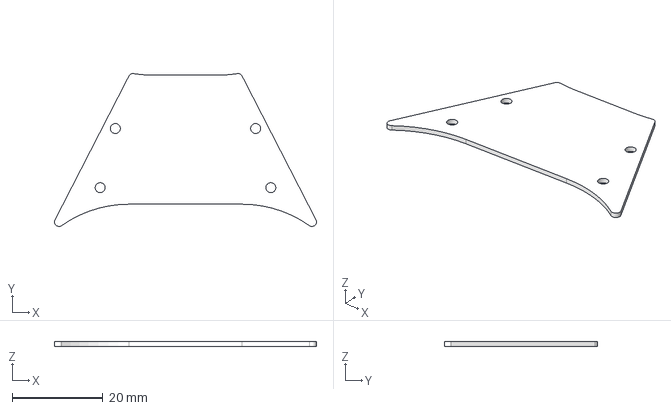
[picture p131: CAD file, 2026-01-11]
ScottoRang/Handwired/Case/ScottoRang - OLED Cover.step
57.8 x 33.7 x 1.00 mm
