joe-scotto/scottokeebs/ScottoRang/PCB/Case/ScottoRang (PCB Edition) - Plate.step

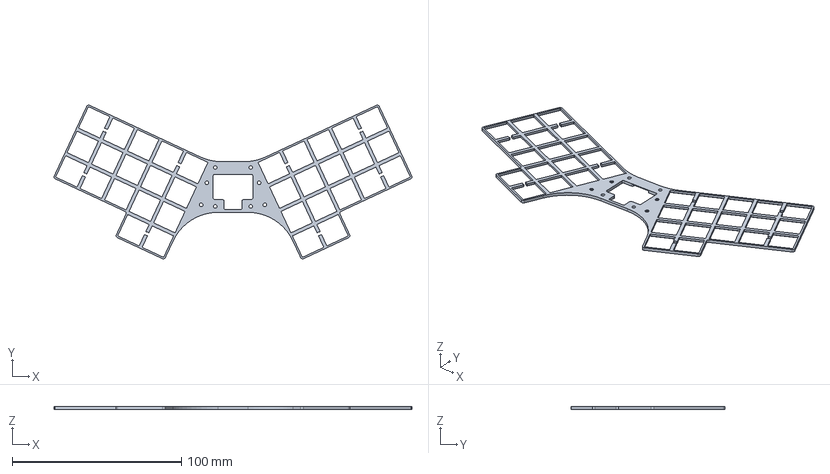
[picture p132: CAD file, 2026-02-11]
ScottoRang/PCB/Case/ScottoRang (PCB Edition) - Plate.step
211.8 x 91.0 x 1.60 mm
