joe-scotto/scottokeebs/ScottoSlant/Handwired/Case/ScottoSlant - Case.step

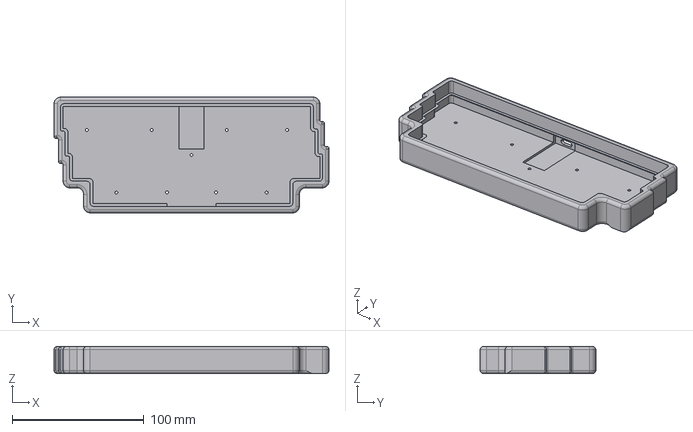
[picture p133: CAD file, 2023-06-10]
ScottoSlant/Handwired/Case/ScottoSlant - Case.step
208.8 x 87.9 x 20.6 mm
