joe-scotto/scottokeebs/ScottoSlant/PCB/Case/ScottoSlant (PCB Edition) - Case.step

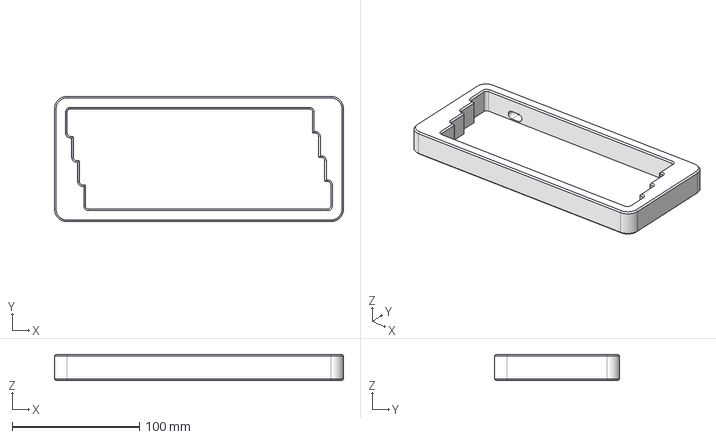
[picture p134: CAD file, 2024-09-14]
ScottoSlant/PCB/Case/ScottoSlant (PCB Edition) - Case.step
227.3 x 98.7 x 20.8 mm
