joe-scotto/scottokeebs/ScottoStarter/Case/ScottoStarter - Plate.step

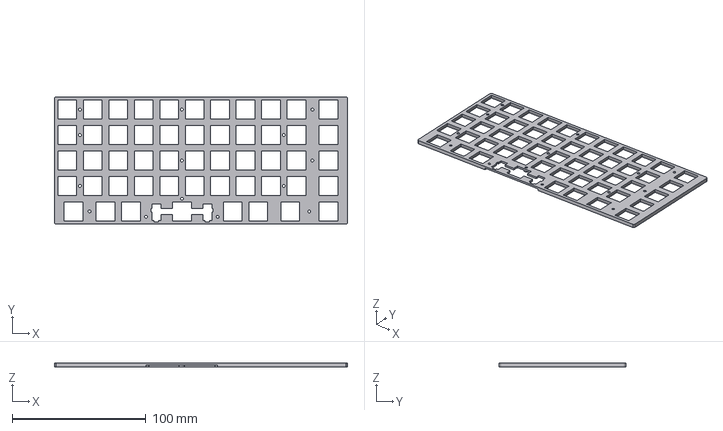
[picture p135: CAD file, 2026-08-03]
ScottoStarter/Case/ScottoStarter - Plate.step
219.1 x 95.2 x 3.00 mm
