joe-scotto/scottokeebs/ScottoT9/Handwired/Case/ScottoT9 - Case.step

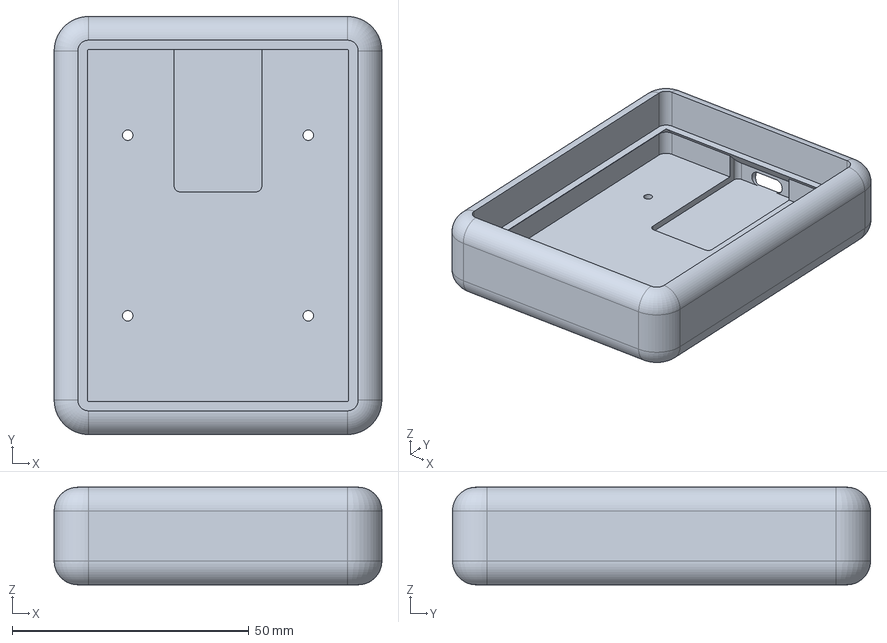
[picture p136: CAD file, 2025-11-11]
ScottoT9/Handwired/Case/ScottoT9 - Case.step
69.2 x 88.2 x 20.6 mm
