joe-scotto/scottokeebs/ScottoT9/PCB/Case/ScottoT9 (PCB Edition) - Plate.step

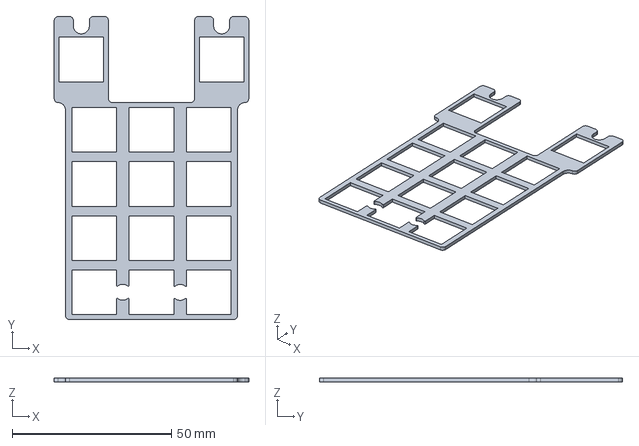
[picture p137: CAD file, 2025-12-09]
ScottoT9/PCB/Case/ScottoT9 (PCB Edition) - Plate.step
61.0 x 95.0 x 1.20 mm
