joe-scotto/scottokeebs/ScottoWing/Handwired/Case/ScottoWing - 3x5 - Middle.step

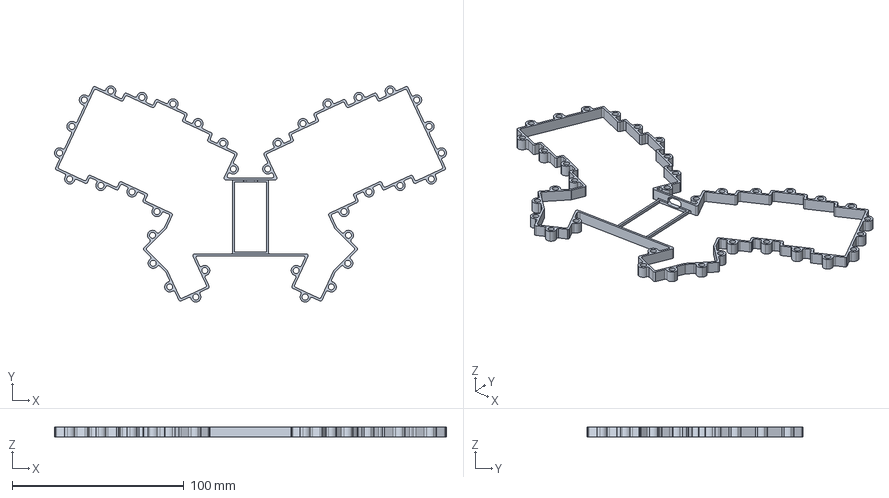
[picture p138: CAD file, 2023-11-20]
ScottoWing/Handwired/Case/ScottoWing - 3x5 - Middle.step
227.9 x 125.7 x 6.00 mm
