joe-scotto/scottokeebs/ScottoWing/PCB/Case/ScottoWing (PCB Edition) - 3x5 (Thick Bezel).step

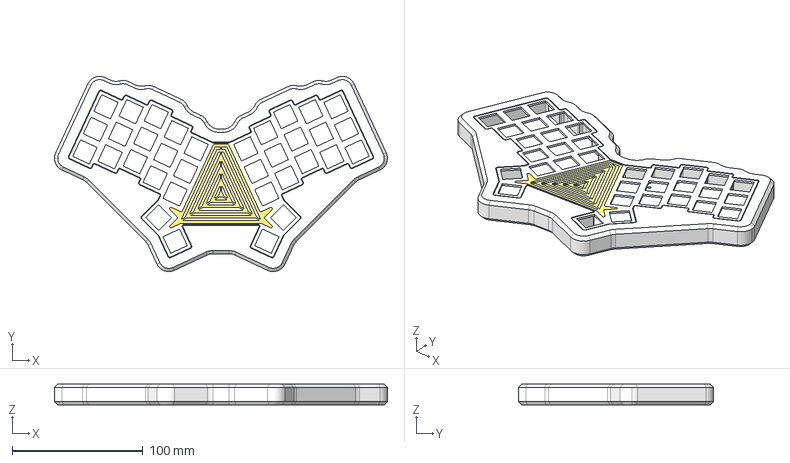
[picture p139: CAD file, 2024-06-16]
ScottoWing/PCB/Case/ScottoWing (PCB Edition) - 3x5 (Thick Bezel).step
255.0 x 149.5 x 15.8 mm
