joe-scotto/scottokeebs/Extras/ScottoBender/ScottoBender - Bottom.step

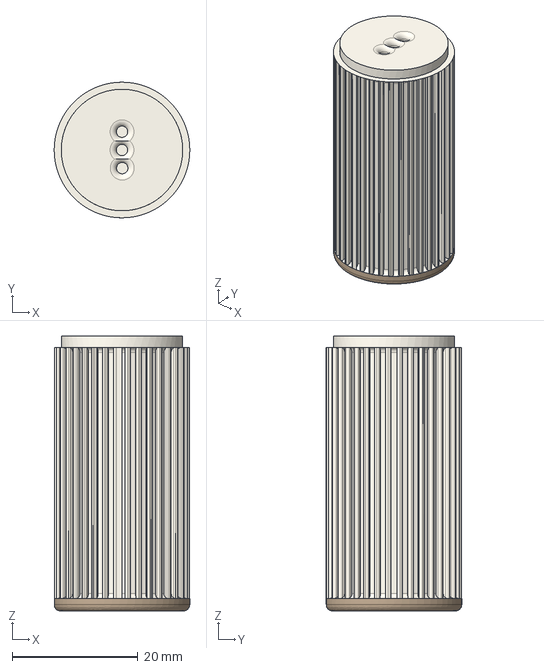
[picture p140: CAD file, 2024-01-28]
Extras/ScottoBender/ScottoBender - Bottom.step
21.6 x 21.6 x 43.8 mm
