joe-scotto/scottokeebs/Extras/ScottoCaps/Flat/Blanks/2.25u.step

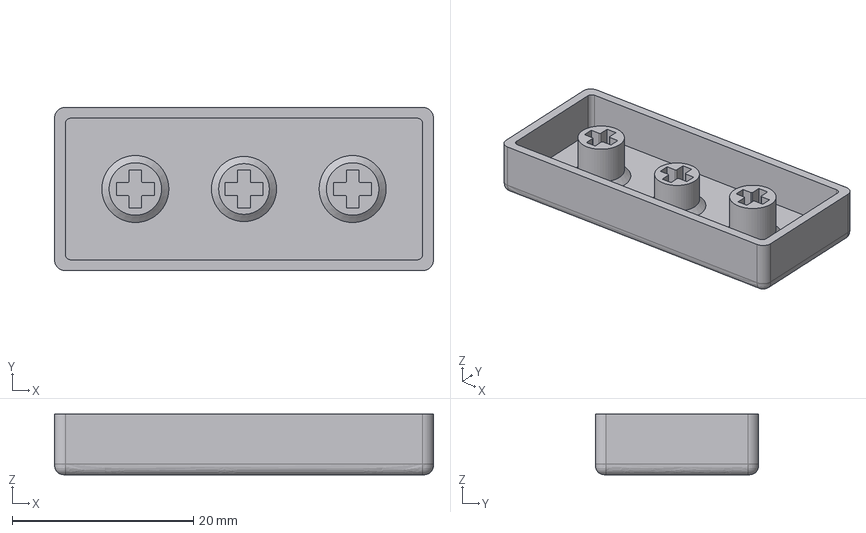
[picture p141: CAD file, 2024-02-25]
Extras/ScottoCaps/Flat/Blanks/2.25u.step
41.9 x 18.0 x 6.70 mm
