joe-scotto/scottokeebs/Extras/ScottoCaps/Flat/Legends/Caps Lock (1.50u).3mf

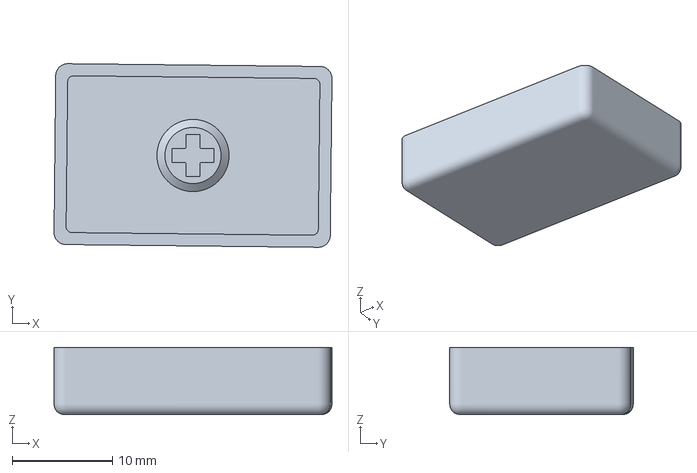
[picture p142: CAD file, 2026-08-05]
Extras/ScottoCaps/Flat/Legends/Caps Lock (1.50u).3mf
27.7 x 18.3 x 6.70 mm
