joe-scotto/scottokeebs/Extras/ScottoCaps/Glass/Choc/ScottoCaps (Glass) - 1.50u.stl

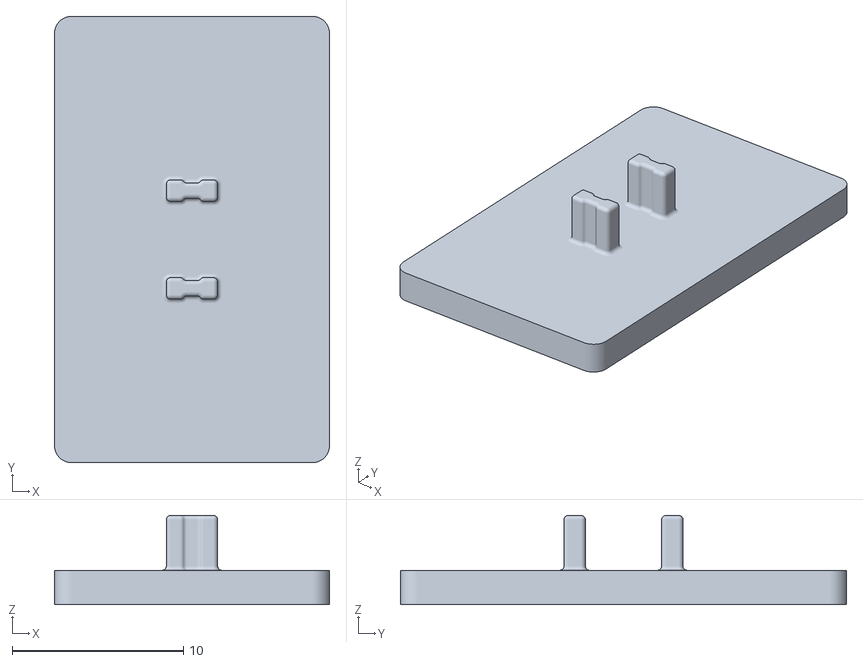
[picture p143: CAD file, 2023-08-21]
Extras/ScottoCaps/Glass/Choc/ScottoCaps (Glass) - 1.50u.stl
16.0 x 26.0 x 5.20
