joe-scotto/scottokeebs/Extras/ScottoCaps/Glass/MX/ScottoCaps (Glass) - 1.75u.step

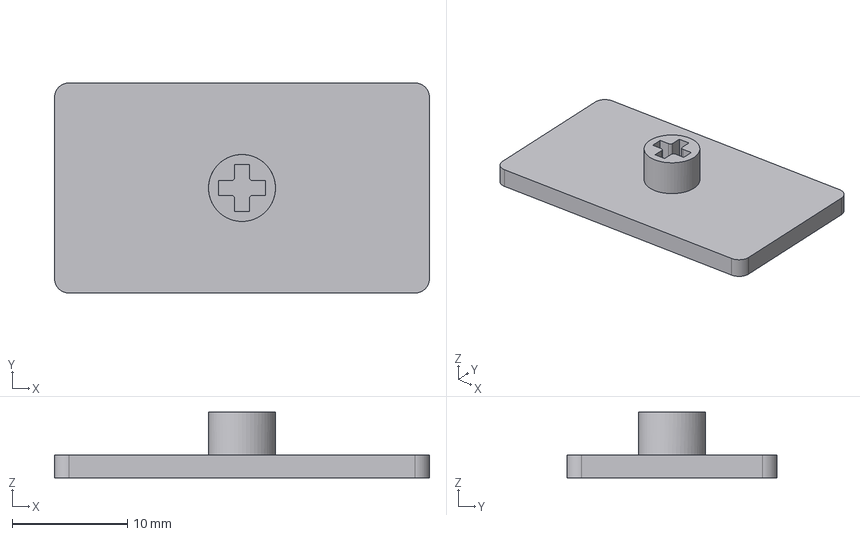
[picture p144: CAD file, 2023-08-16]
Extras/ScottoCaps/Glass/MX/ScottoCaps (Glass) - 1.75u.step
32.5 x 18.2 x 5.70 mm
