joe-scotto/scottokeebs/Extras/ScottoCaps/Scooped/Choc/Blanks/16x16/1.00u (16x16 - Concave).step

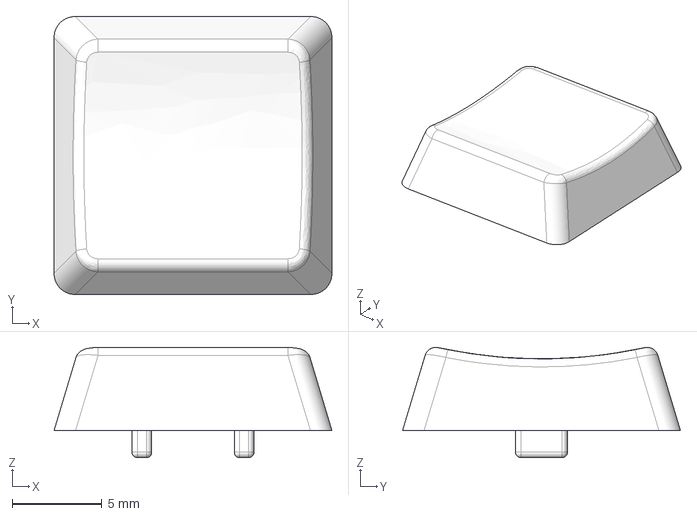
[picture p145: CAD file, 2025-04-24]
Extras/ScottoCaps/Scooped/Choc/Blanks/16x16/1.00u (16x16 - Concave).step
15.5 x 15.5 x 6.14 mm
