joe-scotto/scottokeebs/Extras/ScottoCaps/Scooped/Choc/Blanks/18x17/1.00u (18x17 - Convex).step

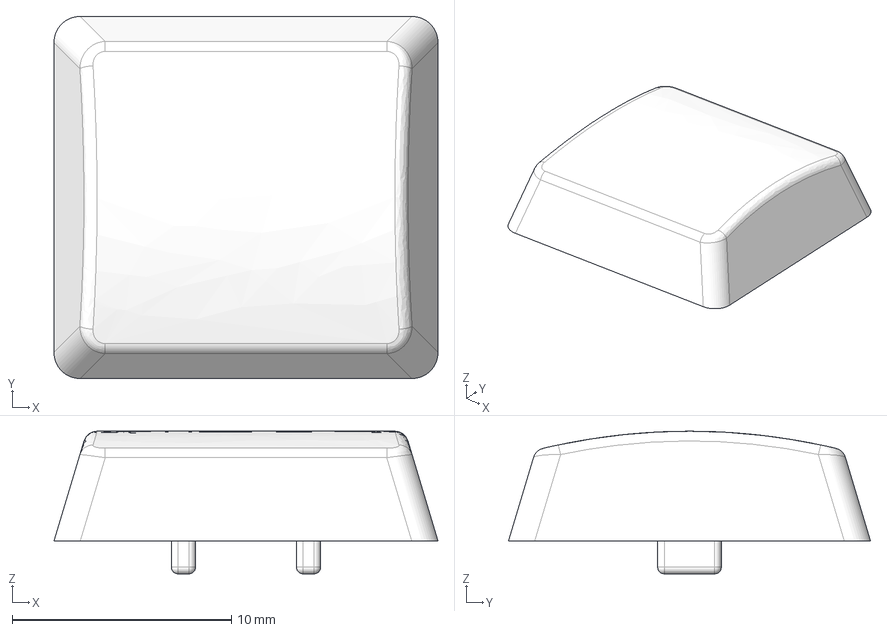
[picture p146: CAD file, 2025-04-24]
Extras/ScottoCaps/Scooped/Choc/Blanks/18x17/1.00u (18x17 - Convex).step
17.5 x 16.5 x 6.50 mm
